abnormal0/3D_Printer/SolidWorks/New/铝型材角码/2020-210-45.SLDPRT

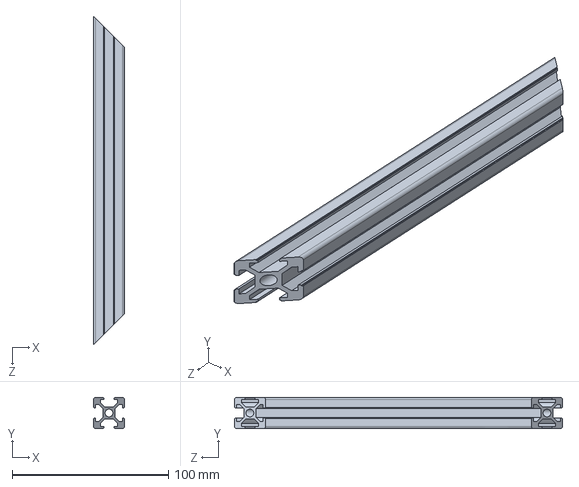
[picture p15: CAD file, 2020-09-15]
SolidWorks/New/铝型材角码/2020-210-45.SLDPRT
20.0 x 20.0 x 210.0 mm
