abnormal0/3D_Printer/SolidWorks/New/螺母座.SLDPRT

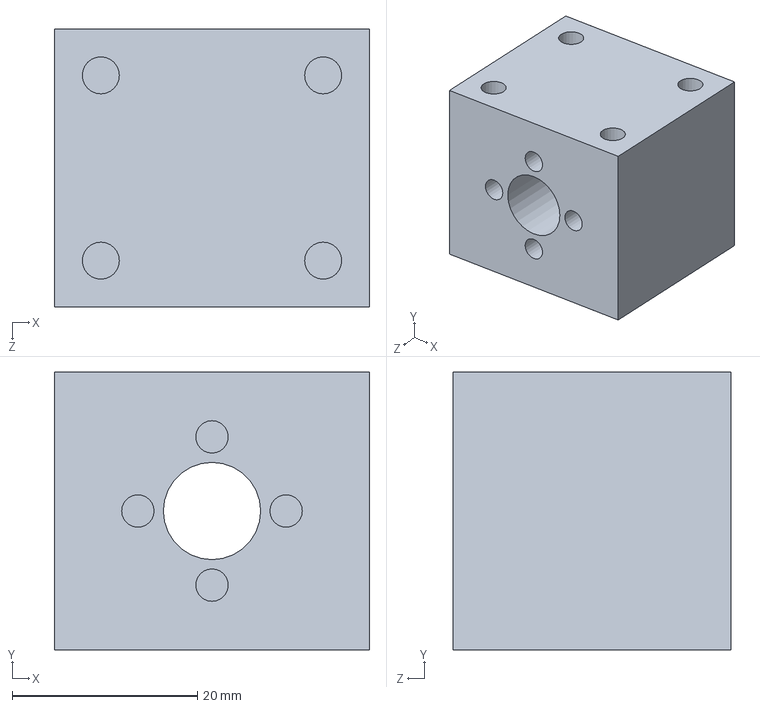
[picture p16: CAD file, 2020-09-15]
SolidWorks/New/螺母座.SLDPRT
34.0 x 30.0 x 30.0 mm
