abnormal0/3D_Printer/SolidWorks/New/铝型材角码/2020-188.SLDPRT

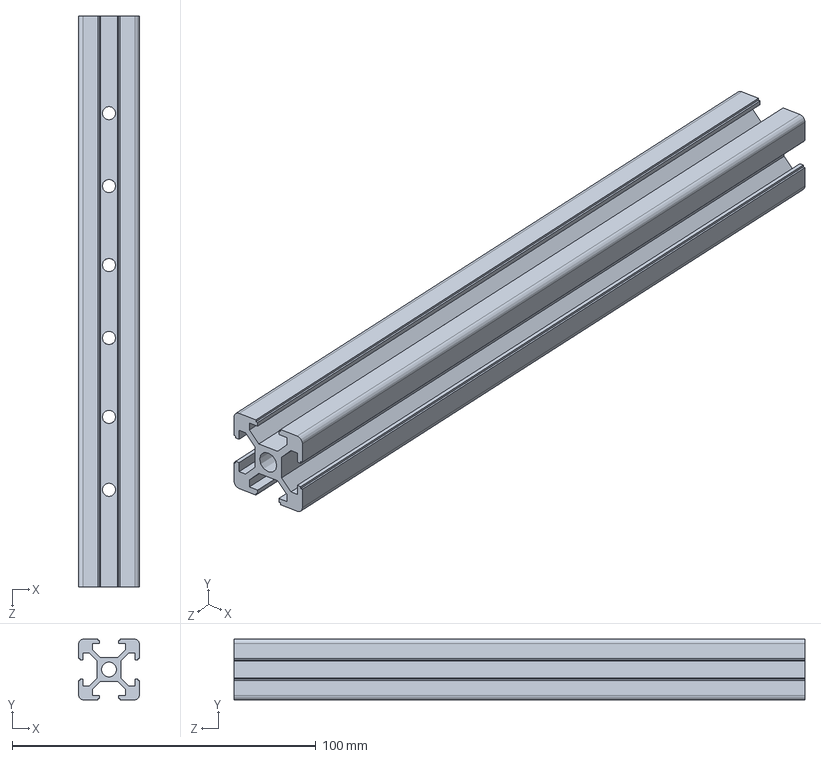
[picture p17: CAD file, 2020-09-15]
SolidWorks/New/铝型材角码/2020-188.SLDPRT
20.0 x 20.0 x 188.0 mm
