abnormal0/3D_Printer/SolidWorks/New/2020角码-45度.SLDPRT

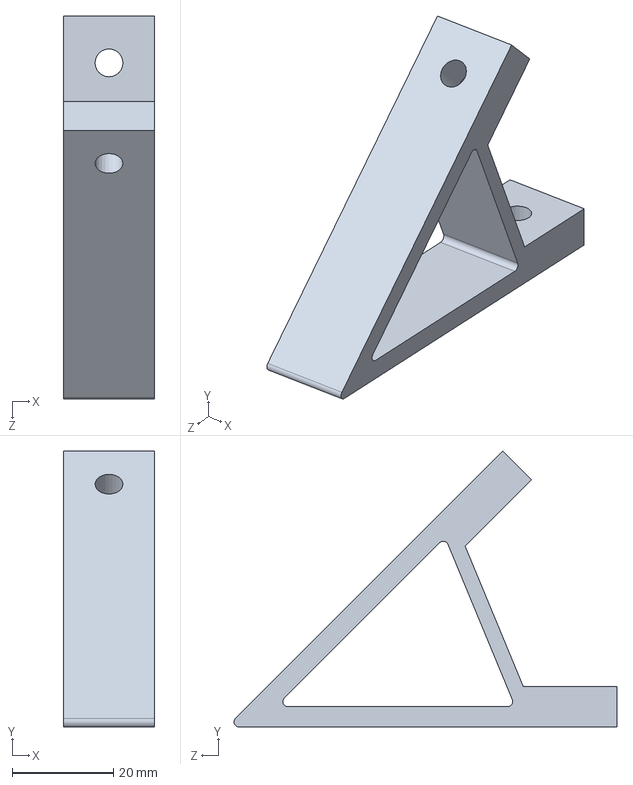
[picture p18: CAD file, 2020-09-15]
SolidWorks/New/2020角码-45度.SLDPRT
18.0 x 54.4 x 75.6 mm
