abnormal0/3D_Printer/SolidWorks/New/铝型材角码/2020-220.SLDPRT

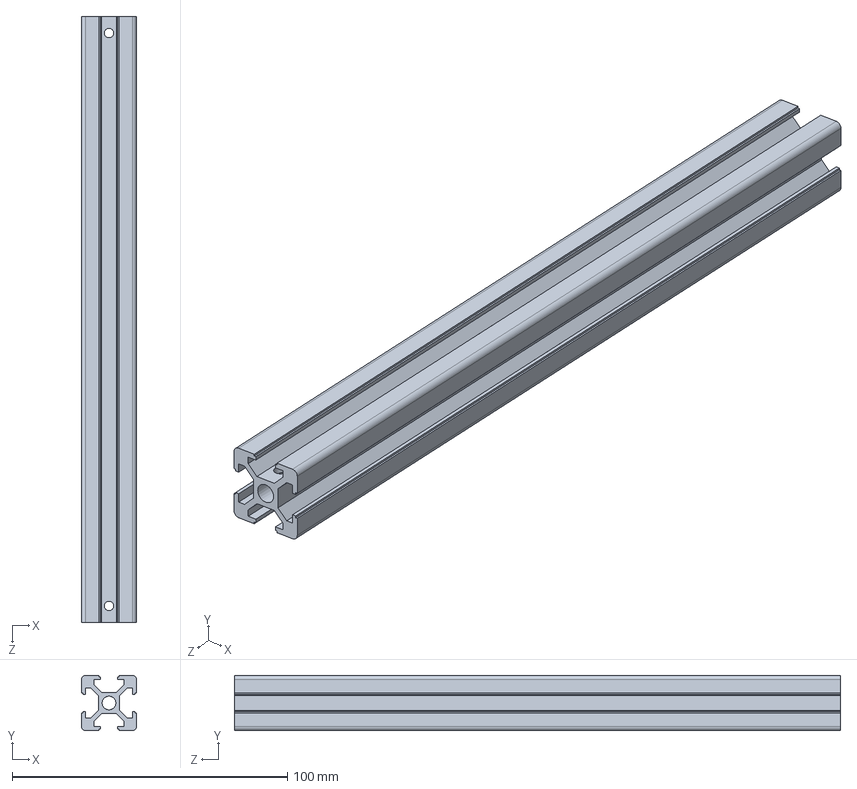
[picture p19: CAD file, 2020-09-15]
SolidWorks/New/铝型材角码/2020-220.SLDPRT
20.0 x 20.0 x 220.0 mm
