abnormal0/3D_Printer/SolidWorks/New/喷头安装座.SLDPRT

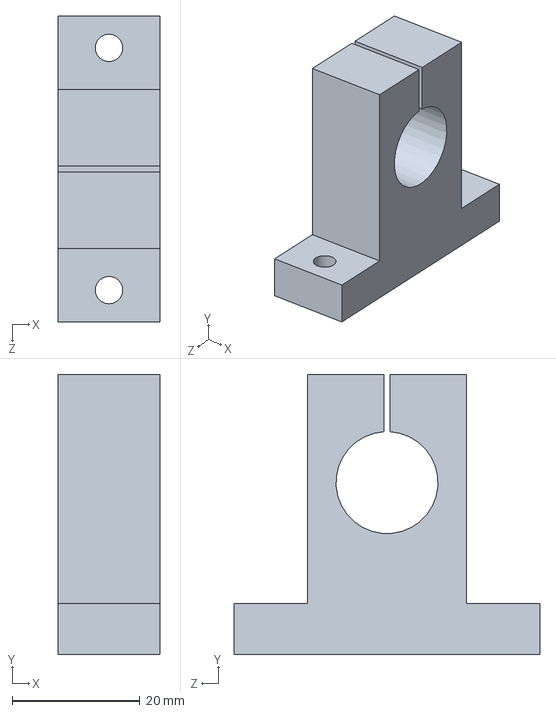
[picture p20: CAD file, 2020-09-15]
SolidWorks/New/喷头安装座.SLDPRT
16.0 x 44.0 x 48.0 mm
