abnormal0/3D_Printer/SolidWorks/New/M3蝶形螺母.SLDPRT

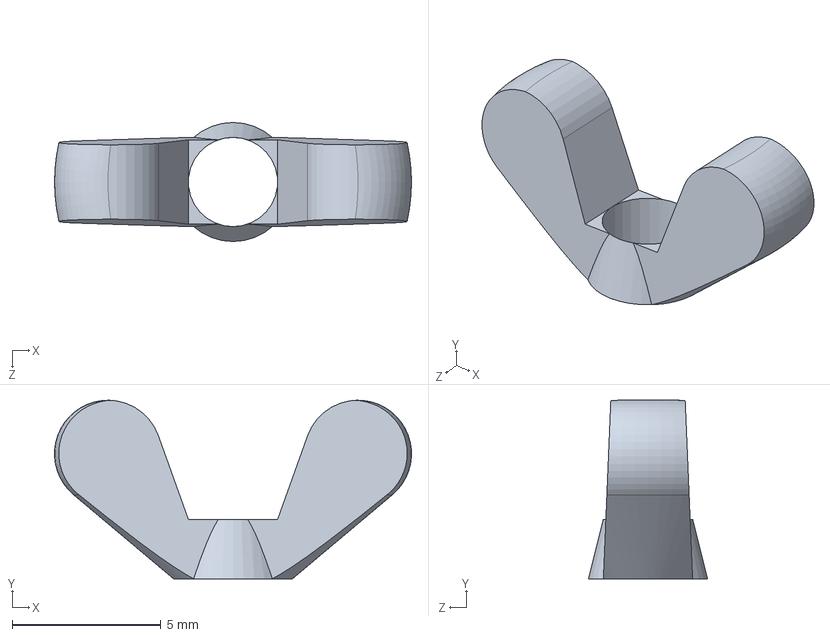
[picture p21: CAD file, 2020-09-15]
SolidWorks/New/M3蝶形螺母.SLDPRT
12.0 x 6.00 x 4.00 mm
