abnormal0/3D_Printer/SolidWorks/New/2GT-20齿同步轮.SLDPRT

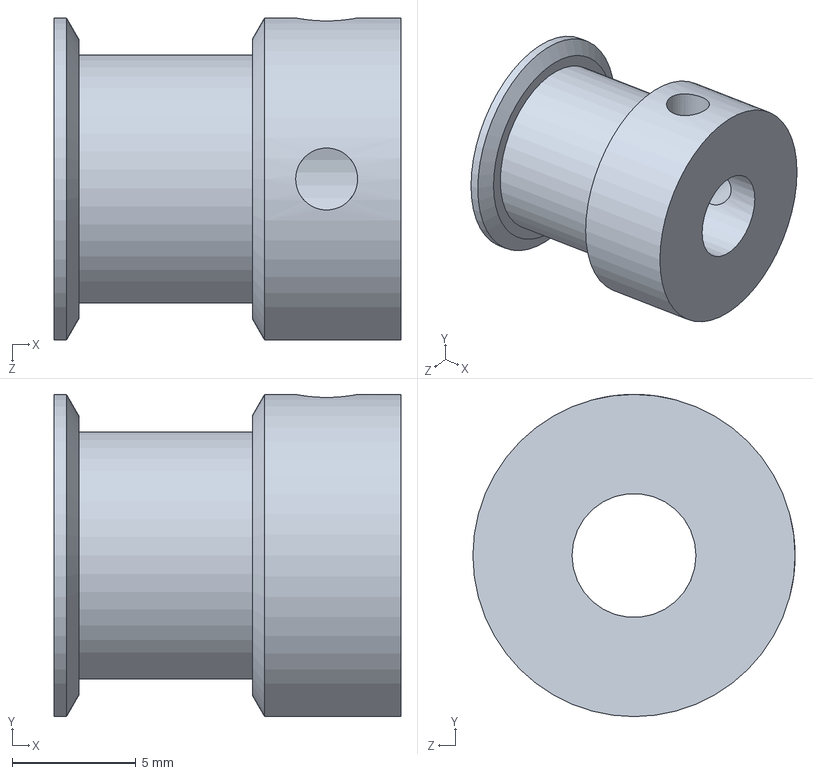
[picture p22: CAD file, 2020-09-15]
SolidWorks/New/2GT-20齿同步轮.SLDPRT
14.0 x 13.0 x 13.0 mm
