abnormal0/3D_Printer/SolidWorks/New/光杆架垫片.SLDPRT

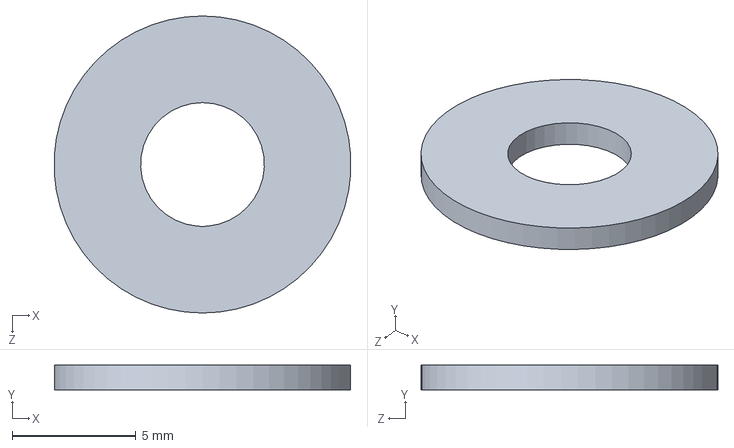
[picture p23: CAD file, 2020-09-15]
SolidWorks/New/光杆架垫片.SLDPRT
12.0 x 1.00 x 12.0 mm
