abnormal0/3D_Printer/SolidWorks/New/立式轴承座左铝片.SLDPRT

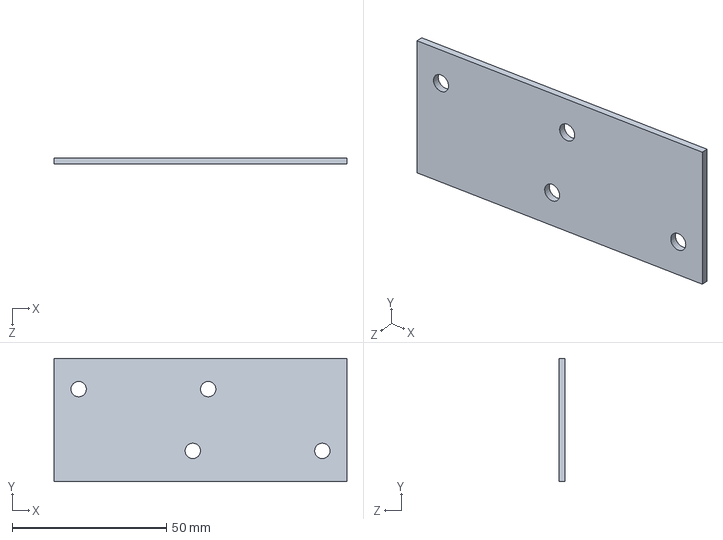
[picture p24: CAD file, 2020-09-15]
SolidWorks/New/立式轴承座左铝片.SLDPRT
95.0 x 40.0 x 2.00 mm
