abnormal0/3D_Printer/SolidWorks/New/小角件.SLDPRT

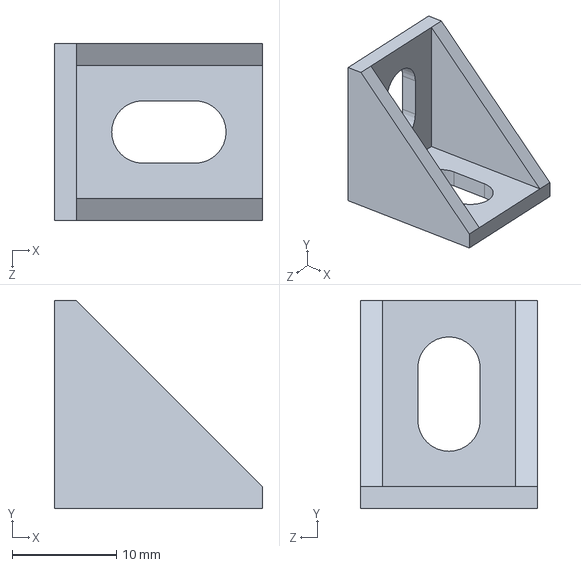
[picture p25: CAD file, 2020-09-15]
SolidWorks/New/小角件.SLDPRT
20.0 x 20.0 x 17.0 mm
