abnormal0/3D_Printer/SolidWorks/New/M3垫片.SLDPRT

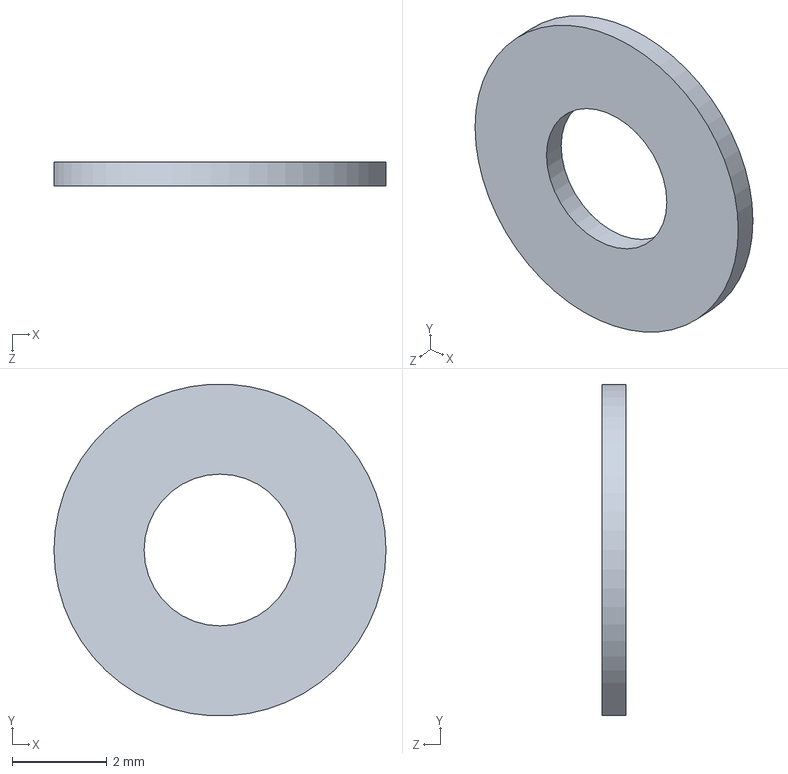
[picture p26: CAD file, 2020-09-15]
SolidWorks/New/M3垫片.SLDPRT
7.00 x 6.99 x 0.5 mm
