abnormal0/3D_Printer/SolidWorks/New/风扇.SLDPRT

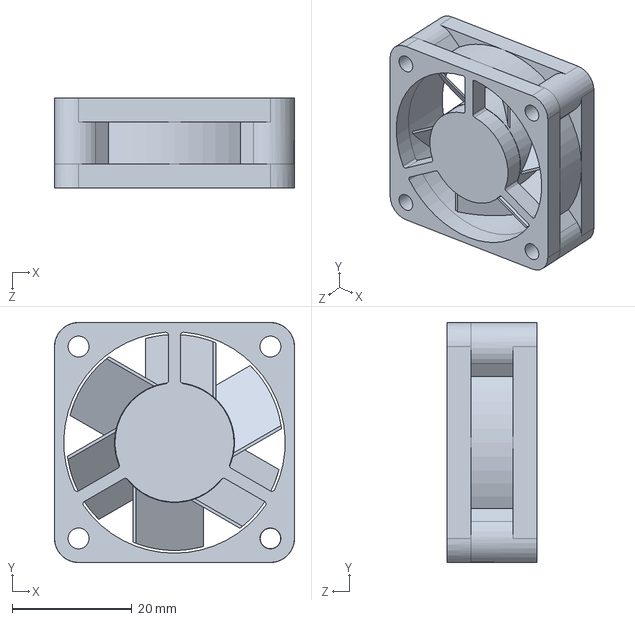
[picture p27: CAD file, 2020-09-15]
SolidWorks/New/风扇.SLDPRT
40.0 x 40.0 x 15.0 mm
