abnormal0/3D_Printer/SolidWorks/New/光电限位开关U型.SLDPRT

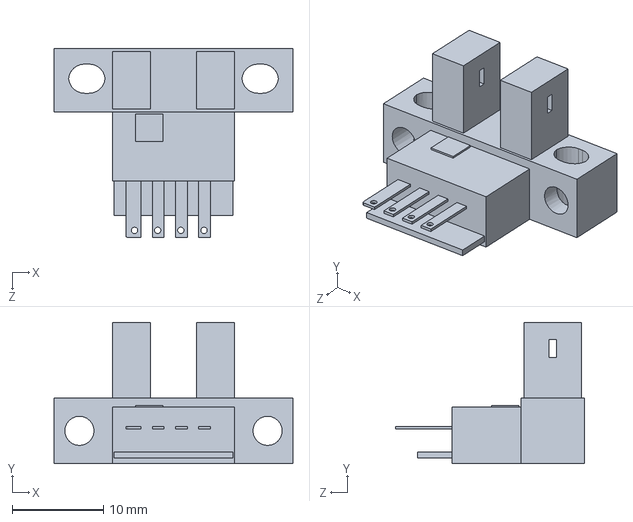
[picture p28: CAD file, 2020-09-15]
SolidWorks/New/光电限位开关U型.SLDPRT
26.2 x 15.5 x 20.7 mm
