abnormal0/3D_Printer/SolidWorks/New/直线轴承.SLDPRT

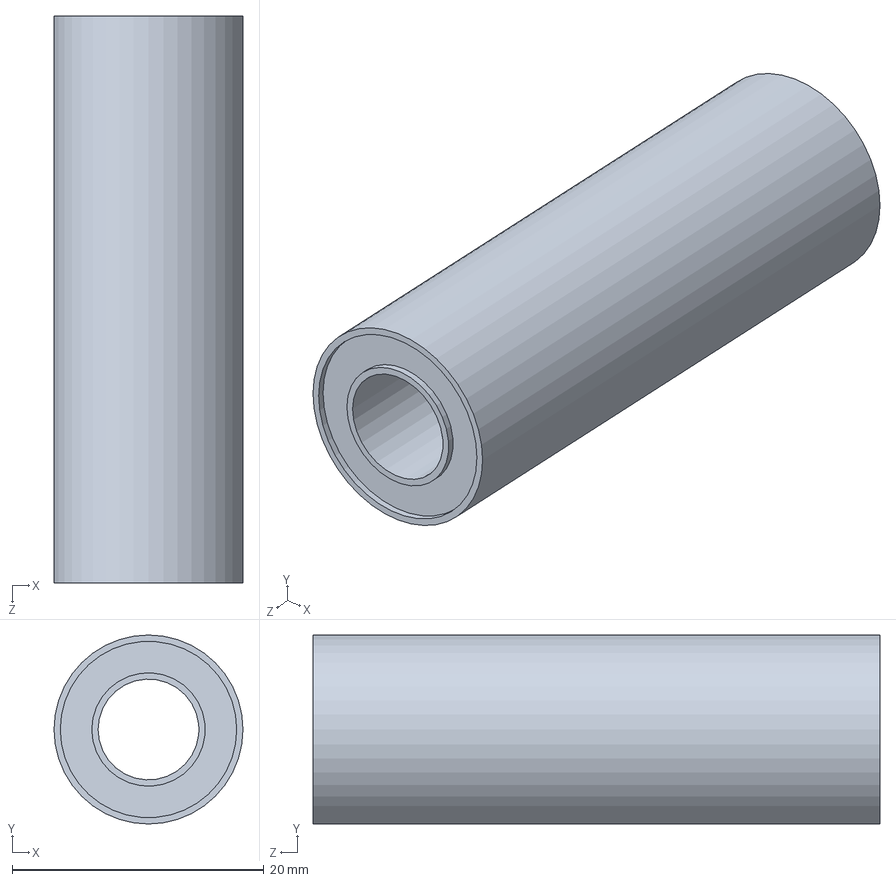
[picture p29: CAD file, 2020-09-15]
SolidWorks/New/直线轴承.SLDPRT
15.0 x 15.0 x 45.0 mm
