abnormal0/3D_Printer/SolidWorks/New/z轴限位片.SLDPRT

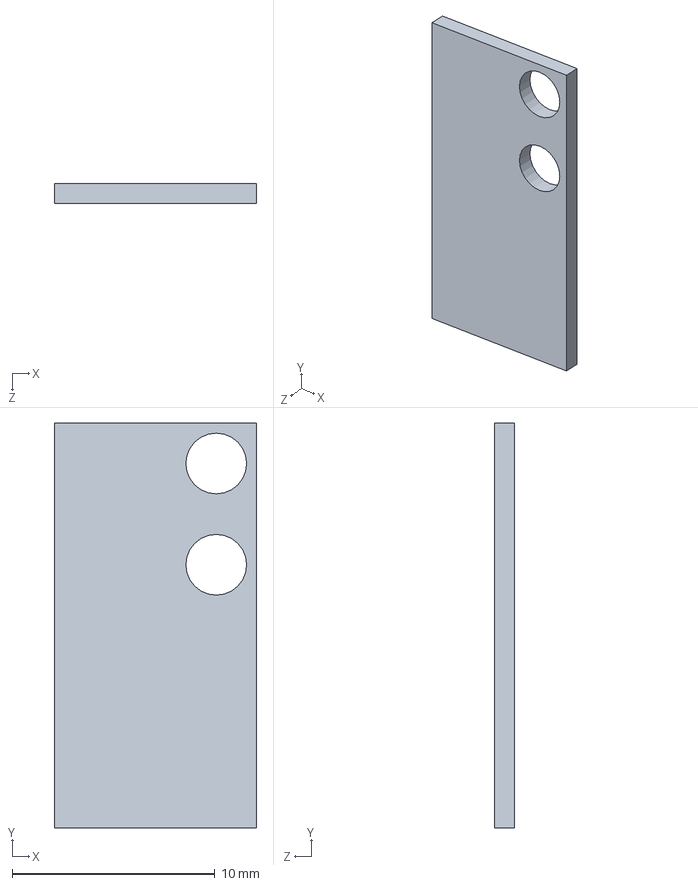
[picture p30: CAD file, 2020-09-15]
SolidWorks/New/z轴限位片.SLDPRT
10.0 x 20.0 x 1.00 mm
