abnormal0/3D_Printer/SolidWorks/New/螺母座z轴限位.SLDPRT

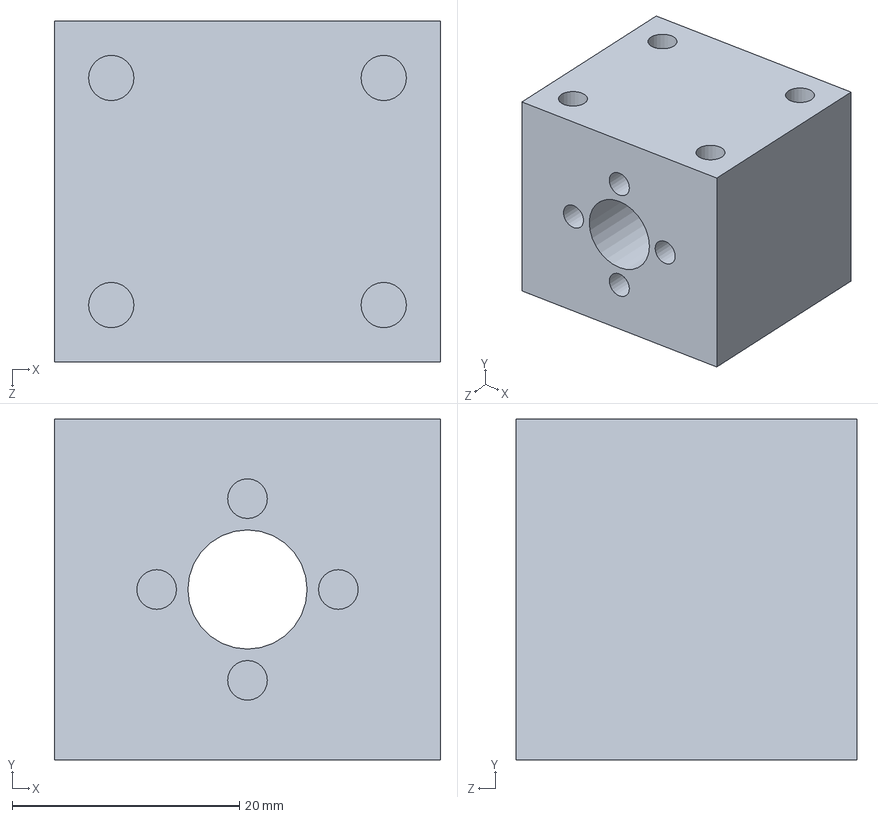
[picture p31: CAD file, 2020-09-15]
SolidWorks/New/螺母座z轴限位.SLDPRT
34.0 x 30.0 x 30.0 mm
