abnormal0/3D_Printer/SolidWorks/New/电机座.SLDPRT

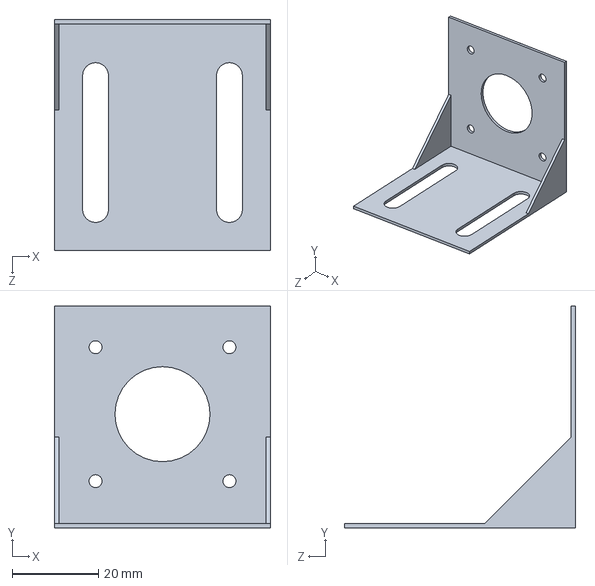
[picture p33: CAD file, 2020-09-15]
SolidWorks/New/电机座.SLDPRT
50.0 x 51.3 x 53.5 mm
