abnormal0/3D_Printer/SolidWorks/New/亚克力主板托盘.SLDPRT

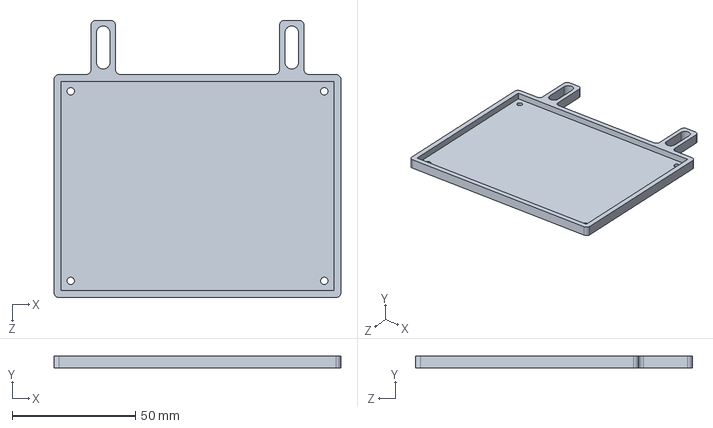
[picture p34: CAD file, 2020-09-15]
SolidWorks/New/亚克力主板托盘.SLDPRT
116.6 x 5.00 x 112.6 mm
