abnormal0/3D_Printer/SolidWorks/New/散热管.SLDPRT

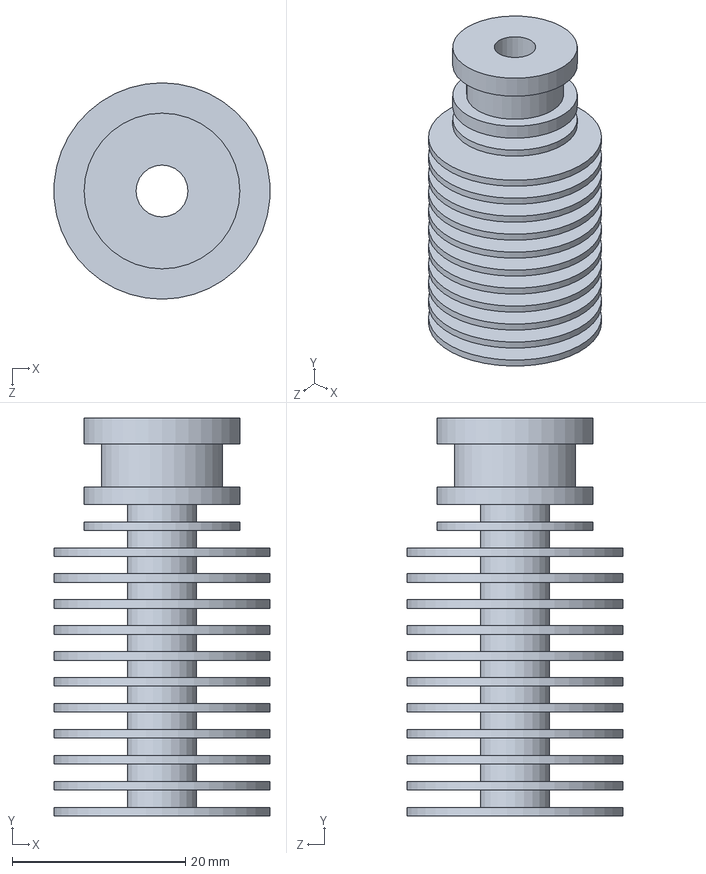
[picture p35: CAD file, 2020-09-15]
SolidWorks/New/散热管.SLDPRT
24.9 x 46.0 x 25.0 mm
