abnormal0/3D_Printer/SolidWorks/New/热床.SLDPRT

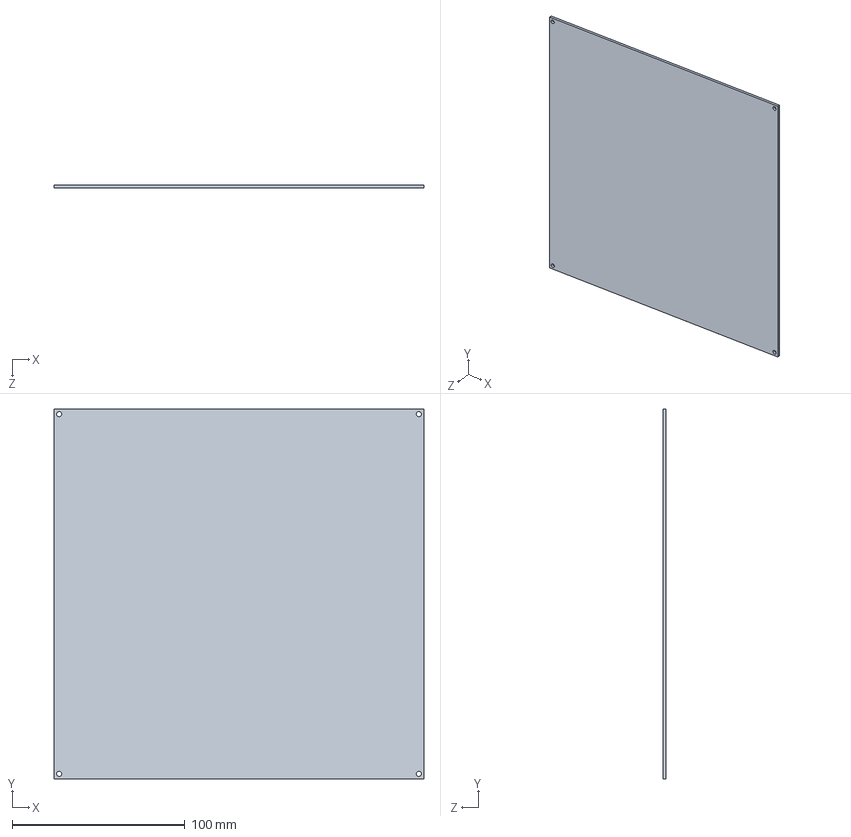
[picture p36: CAD file, 2020-09-15]
SolidWorks/New/热床.SLDPRT
214.0 x 214.0 x 2.00 mm
