abnormal0/3D_Printer/SolidWorks/New/直线轴承圆法兰.SLDPRT

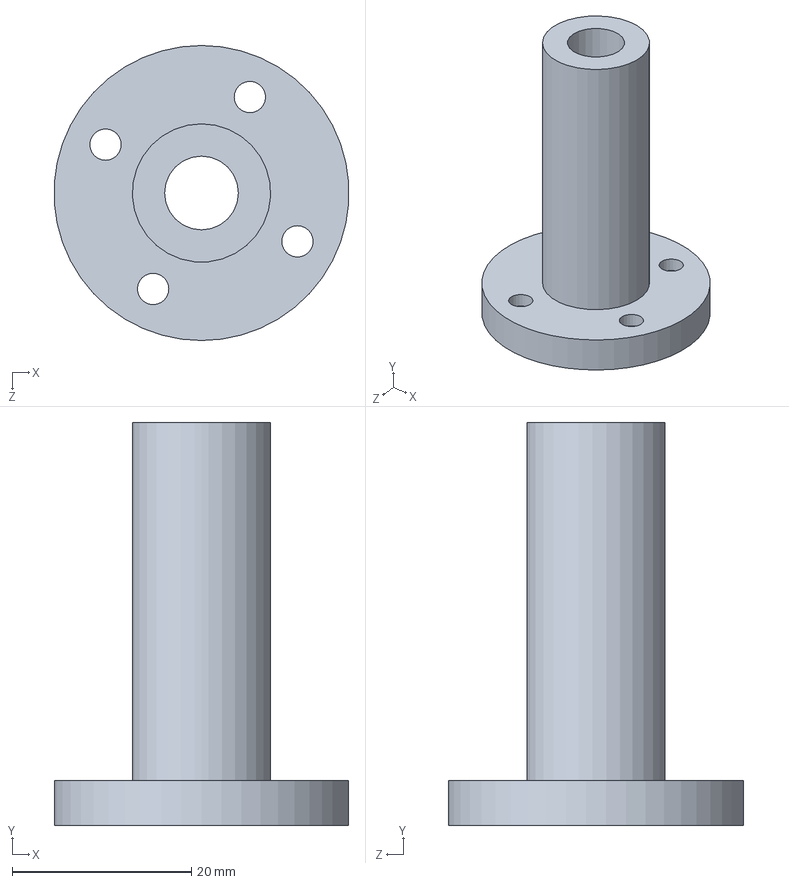
[picture p37: CAD file, 2020-09-15]
SolidWorks/New/直线轴承圆法兰.SLDPRT
32.9 x 45.0 x 32.9 mm
