abnormal0/3D_Printer/SolidWorks/New/丝轴z轴（无螺纹）.SLDPRT

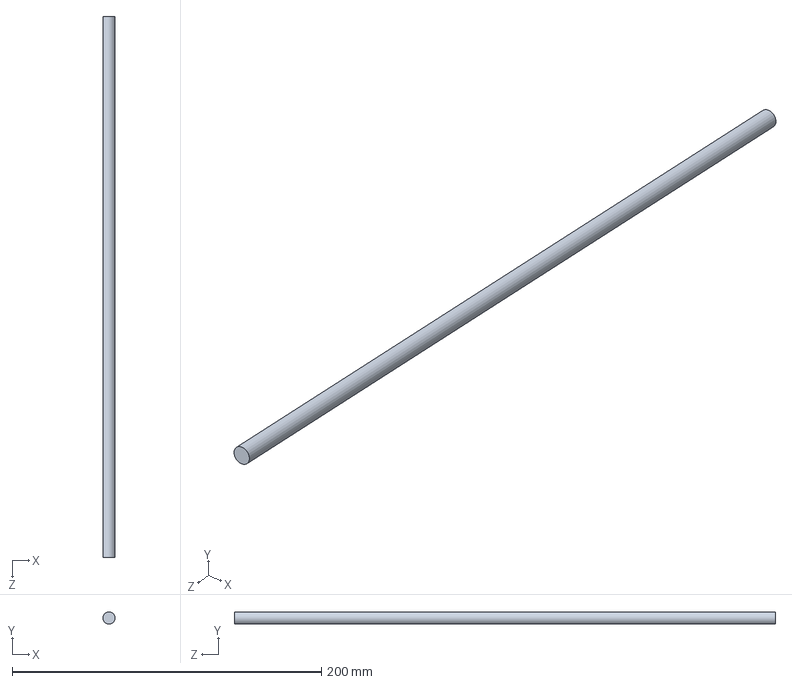
[picture p38: CAD file, 2020-09-15]
SolidWorks/New/丝轴z轴（无螺纹）.SLDPRT
8.00 x 8.00 x 350.0 mm
