abnormal0/3D_Printer/SolidWorks/New/M3_外六角螺丝.SLDPRT

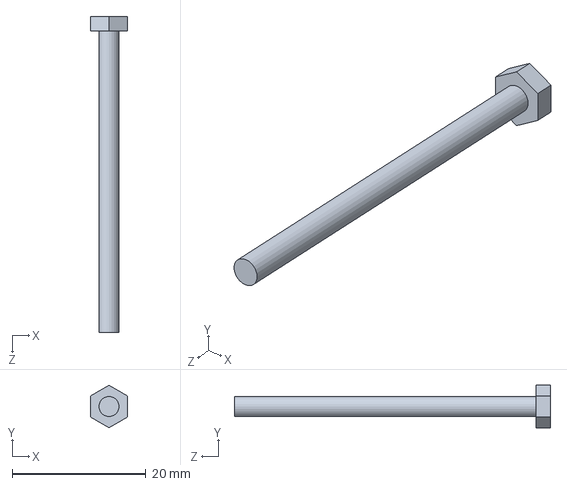
[picture p39: CAD file, 2020-09-15]
SolidWorks/New/M3_外六角螺丝.SLDPRT
5.50 x 6.35 x 47.2 mm
