abnormal0/3D_Printer/SolidWorks/New/2040-420.SLDPRT

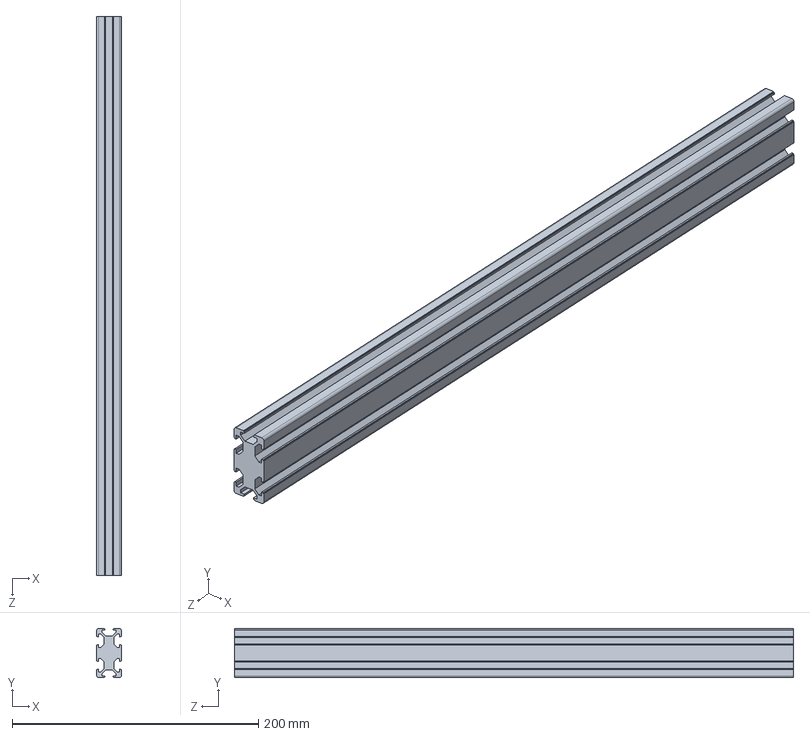
[picture p40: CAD file, 2020-09-15]
SolidWorks/New/2040-420.SLDPRT
20.0 x 40.0 x 454.0 mm
