abnormal0/3D_Printer/SolidWorks/New/M4船型螺母.SLDPRT

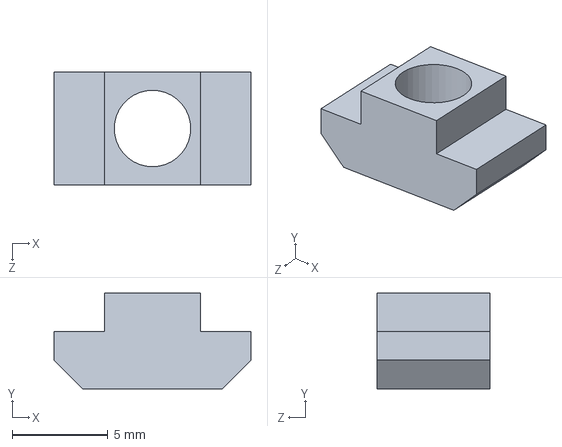
[picture p41: CAD file, 2020-09-15]
SolidWorks/New/M4船型螺母.SLDPRT
10.3 x 5.00 x 5.90 mm
