abnormal0/3D_Printer/SolidWorks/New/x轴铝片.SLDPRT

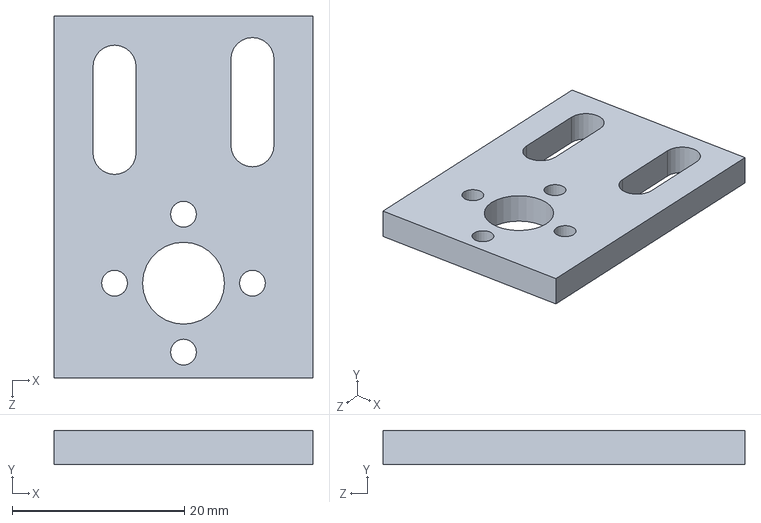
[picture p42: CAD file, 2020-09-15]
SolidWorks/New/x轴铝片.SLDPRT
30.0 x 4.00 x 42.0 mm
