abnormal0/3D_Printer/SolidWorks/New/同步带.SLDPRT

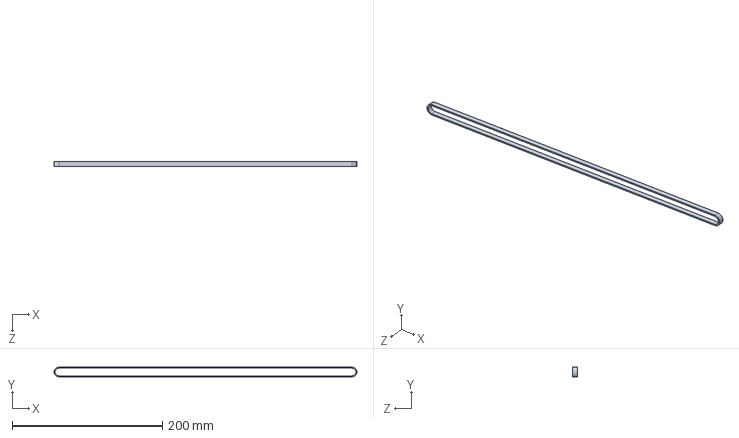
[picture p43: CAD file, 2020-09-15]
SolidWorks/New/同步带.SLDPRT
403.0 x 13.0 x 6.00 mm
