abnormal0/3D_Printer/SolidWorks/New/角铝.SLDPRT

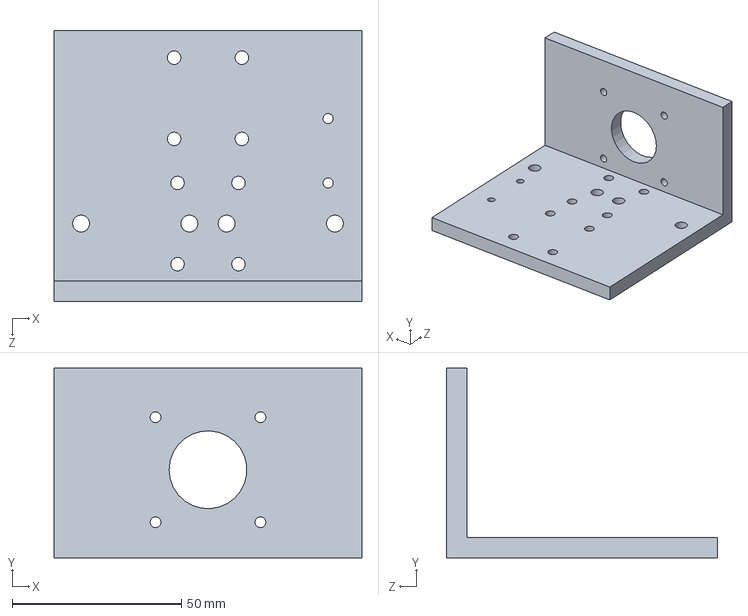
[picture p44: CAD file, 2020-09-15]
SolidWorks/New/角铝.SLDPRT
91.0 x 56.0 x 80.0 mm
