abnormal0/3D_Printer/SolidWorks/New/光杆架.SLDPRT

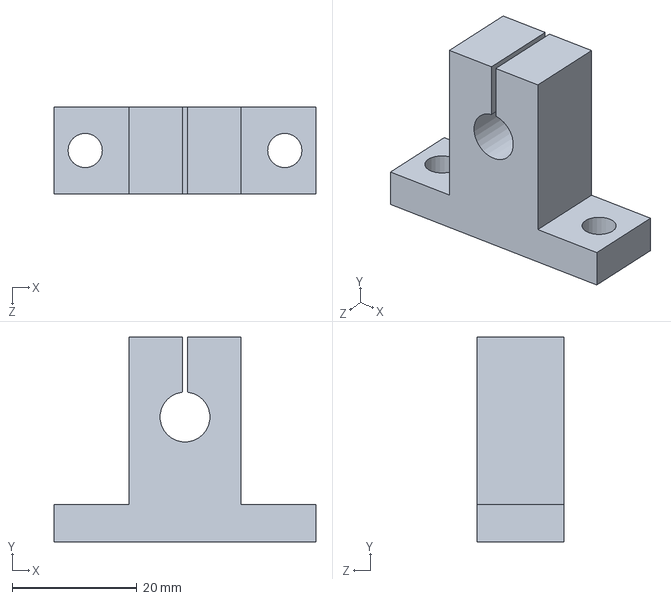
[picture p45: CAD file, 2020-09-15]
SolidWorks/New/光杆架.SLDPRT
42.0 x 32.8 x 14.0 mm
