abnormal0/3D_Printer/SolidWorks/New/42固定铝型材.SLDPRT

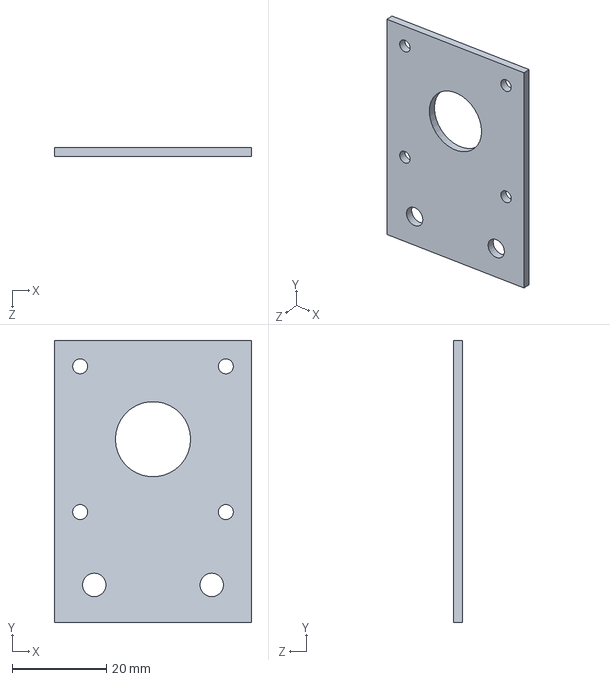
[picture p46: CAD file, 2020-09-15]
SolidWorks/New/42固定铝型材.SLDPRT
42.0 x 60.0 x 2.00 mm
