abnormal0/3D_Printer/SolidWorks/New/角铝中间.SLDPRT

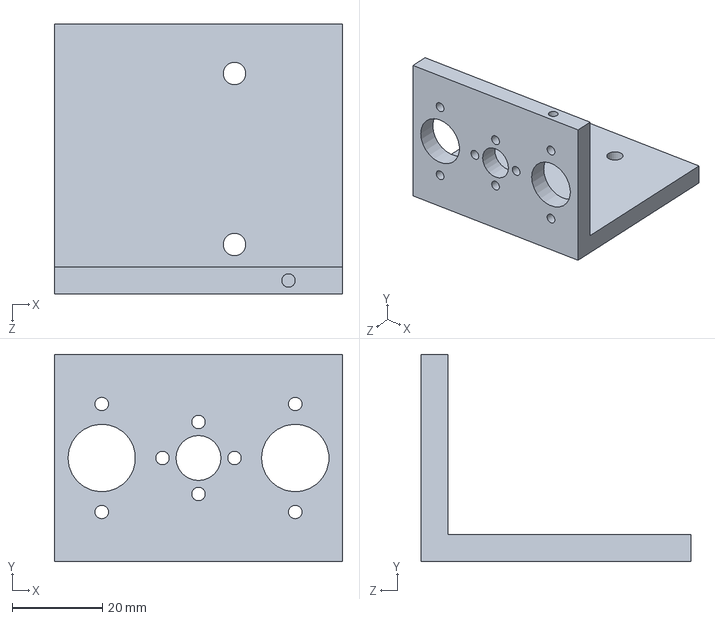
[picture p47: CAD file, 2020-09-15]
SolidWorks/New/角铝中间.SLDPRT
64.0 x 46.0 x 60.0 mm
