abnormal0/3D_Printer/SolidWorks/New/2020角码.SLDPRT

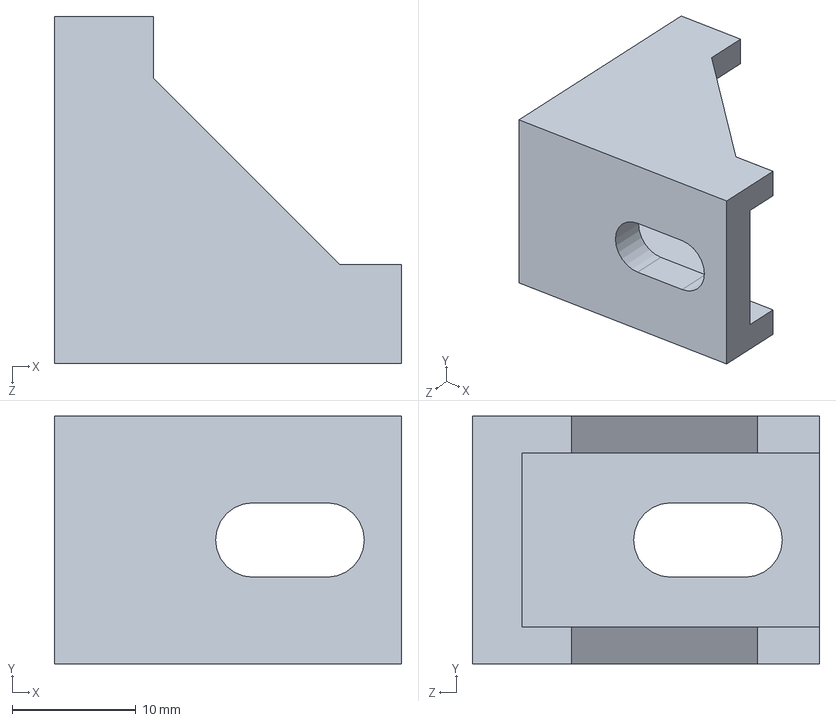
[picture p48: CAD file, 2020-09-15]
SolidWorks/New/2020角码.SLDPRT
28.0 x 20.0 x 28.0 mm
