abnormal0/3D_Printer/SolidWorks/New/喷嘴固定件.SLDPRT

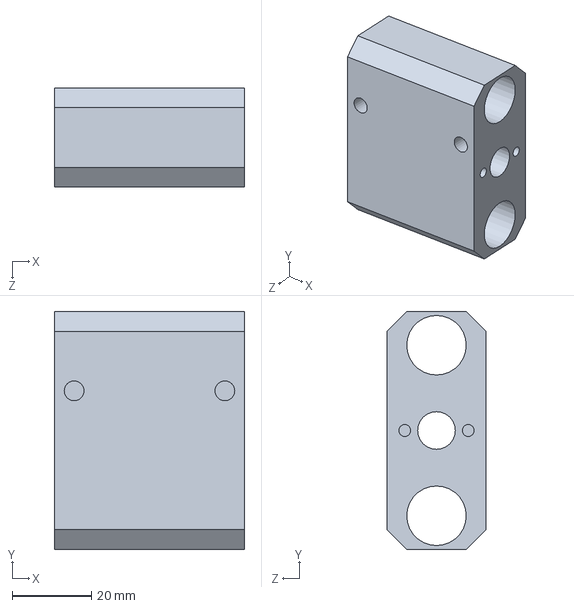
[picture p49: CAD file, 2020-09-15]
SolidWorks/New/喷嘴固定件.SLDPRT
48.0 x 60.0 x 25.0 mm
