abnormal0/3D_Printer/SolidWorks/New/卧式轴承座.SLDPRT

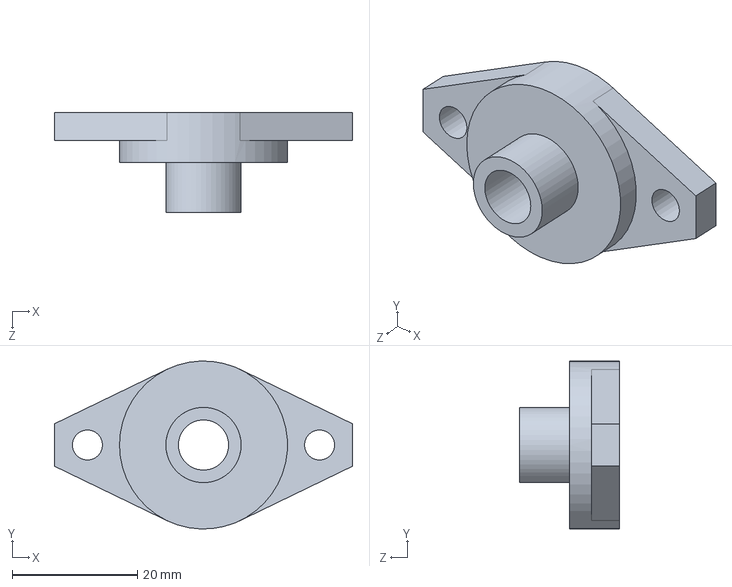
[picture p52: CAD file, 2020-09-15]
SolidWorks/New/卧式轴承座.SLDPRT
47.5 x 26.8 x 16.0 mm
