abnormal0/3D_Printer/SolidWorks/New/加热块.SLDPRT

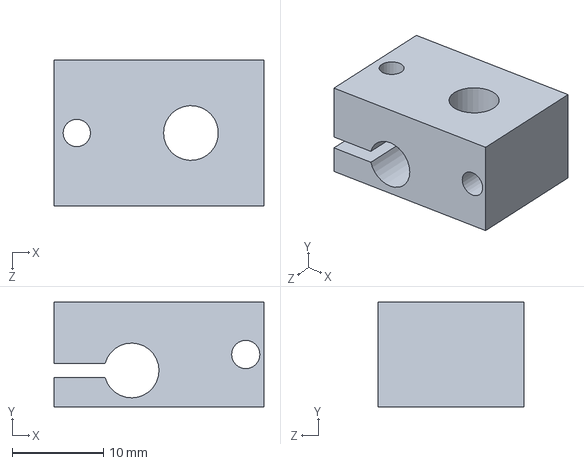
[picture p53: CAD file, 2020-09-15]
SolidWorks/New/加热块.SLDPRT
23.0 x 11.5 x 16.0 mm
