abnormal0/3D_Printer/SolidWorks/New/2020-300.SLDPRT

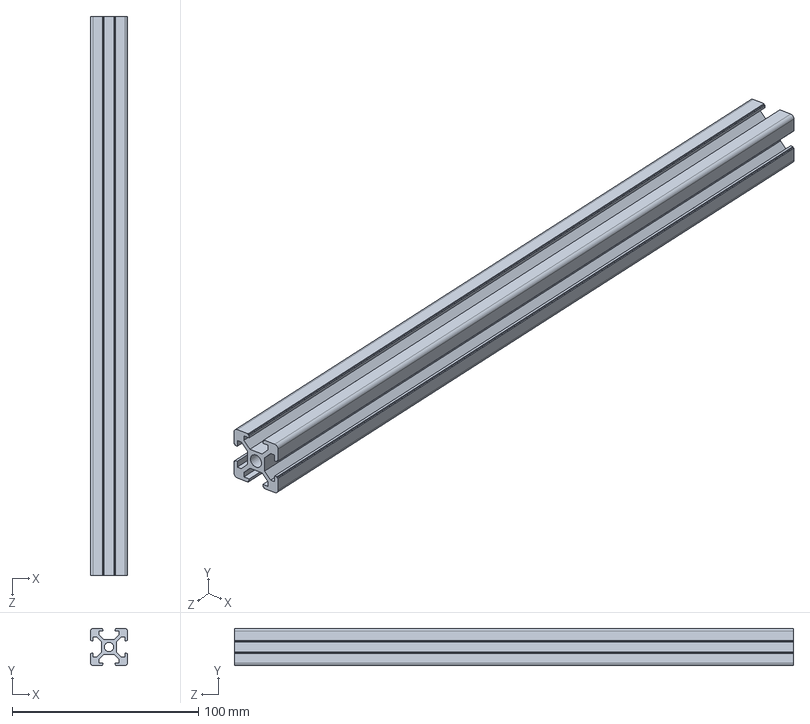
[picture p54: CAD file, 2020-09-15]
SolidWorks/New/2020-300.SLDPRT
20.0 x 20.0 x 300.0 mm
