abnormal0/3D_Printer/SolidWorks/New/光杆x轴.SLDPRT

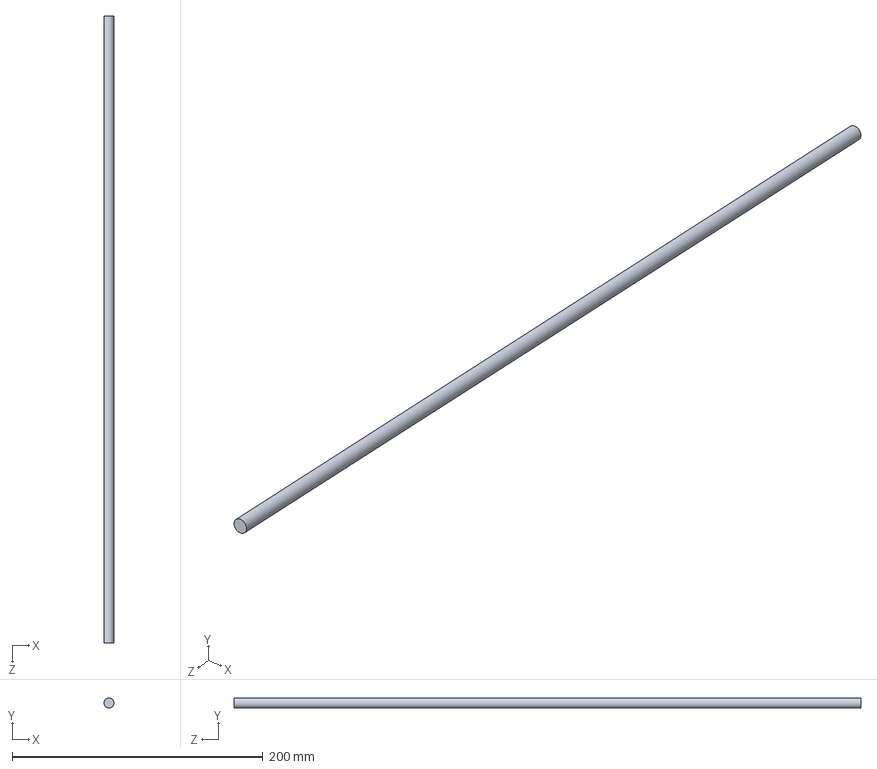
[picture p55: CAD file, 2020-09-15]
SolidWorks/New/光杆x轴.SLDPRT
8.00 x 8.00 x 500.0 mm
