abnormal0/3D_Printer/SolidWorks/New/2020-290.SLDPRT

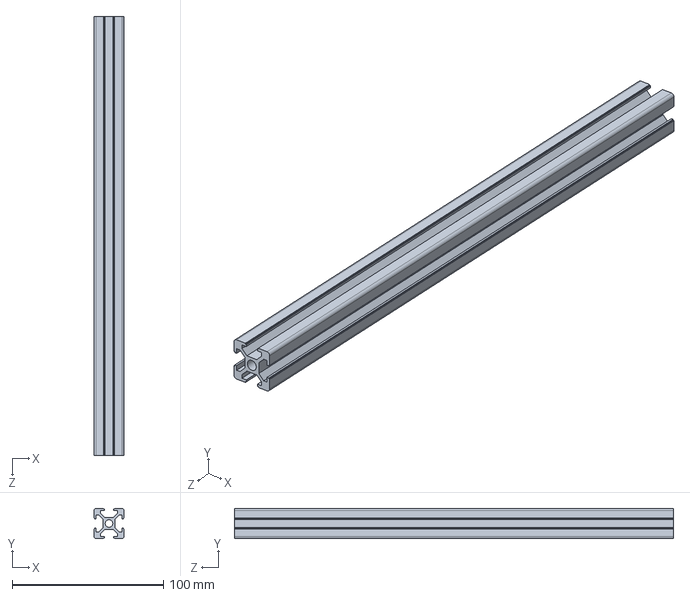
[picture p56: CAD file, 2020-09-15]
SolidWorks/New/2020-290.SLDPRT
20.0 x 20.0 x 290.0 mm
