abnormal0/3D_Printer/SolidWorks/New/42 motor.SLDPRT

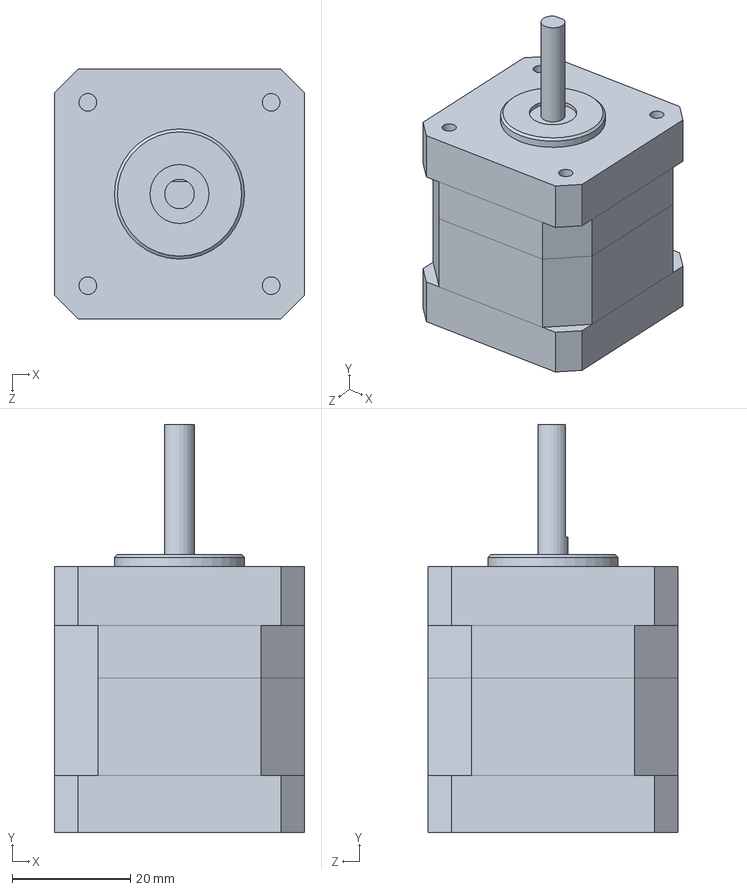
[picture p57: CAD file, 2020-09-15]
SolidWorks/New/42 motor.SLDPRT
42.3 x 69.0 x 42.3 mm
