abnormal0/3D_Printer/SolidWorks/New/风扇3010.SLDPRT

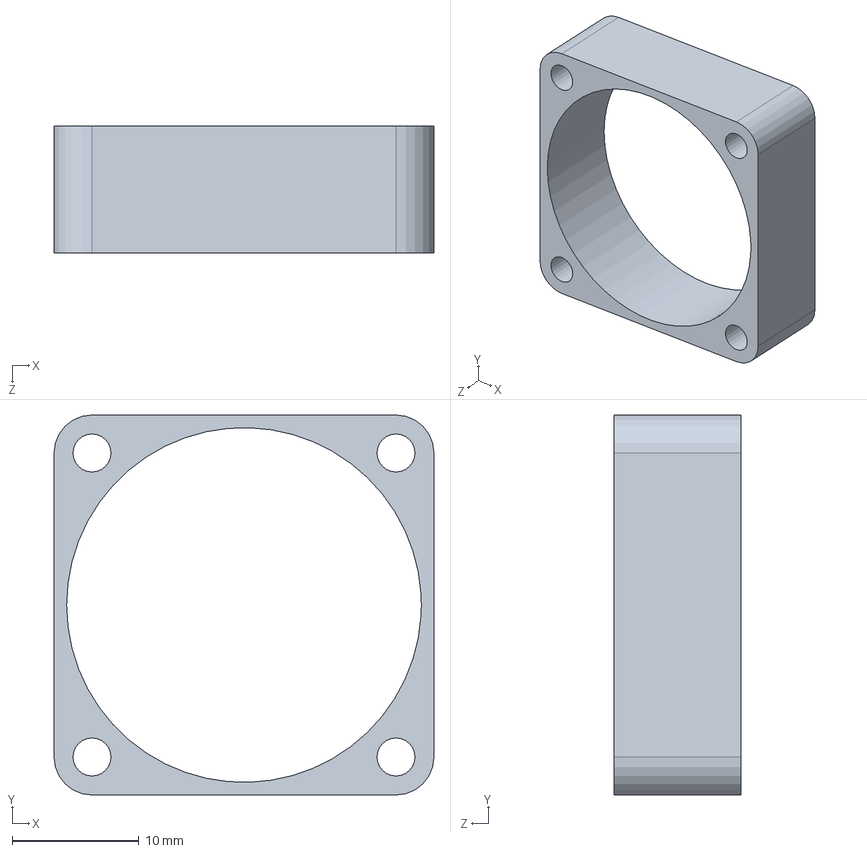
[picture p58: CAD file, 2020-09-15]
SolidWorks/New/风扇3010.SLDPRT
30.0 x 30.0 x 10.0 mm
