abnormal0/3D_Printer/SolidWorks/New/丝杆螺母.SLDPRT

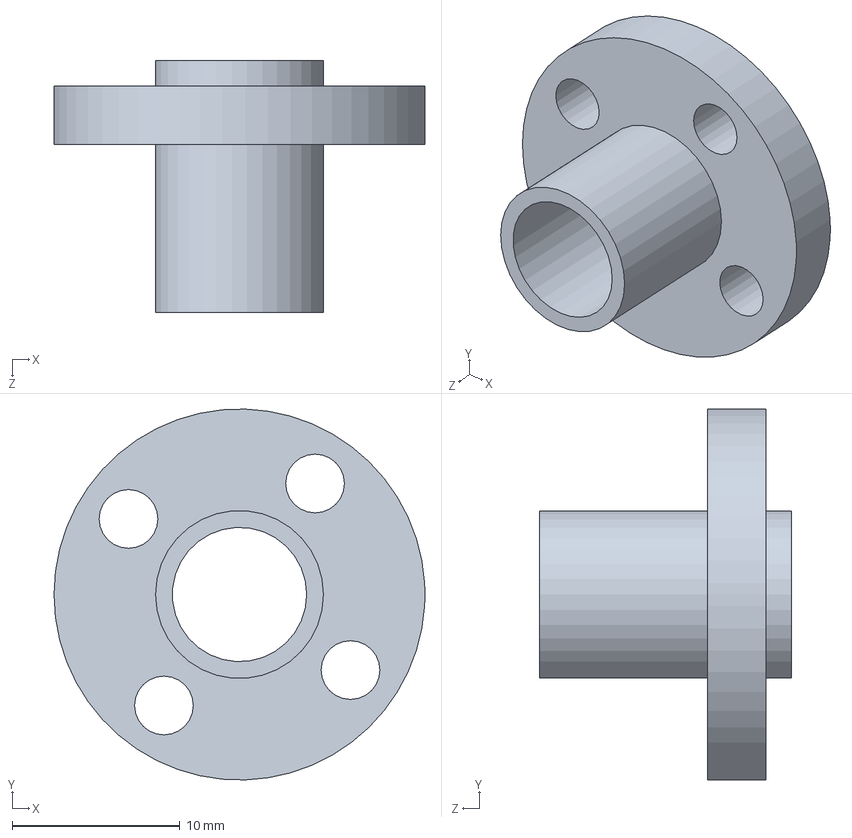
[picture p59: CAD file, 2020-09-15]
SolidWorks/New/丝杆螺母.SLDPRT
22.1 x 22.1 x 15.0 mm
