abnormal0/3D_Printer/SolidWorks/New/椭圆直线轴承.SLDPRT

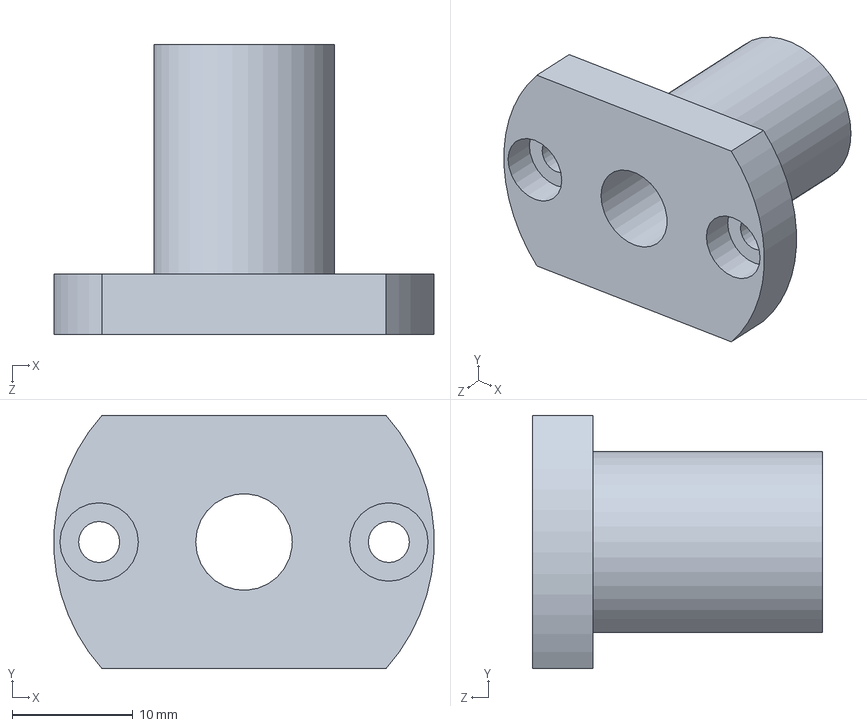
[picture p60: CAD file, 2020-09-15]
SolidWorks/New/椭圆直线轴承.SLDPRT
31.5 x 21.0 x 24.0 mm
