abnormal0/3D_Printer/SolidWorks/New/玻璃板200-200-4.SLDPRT

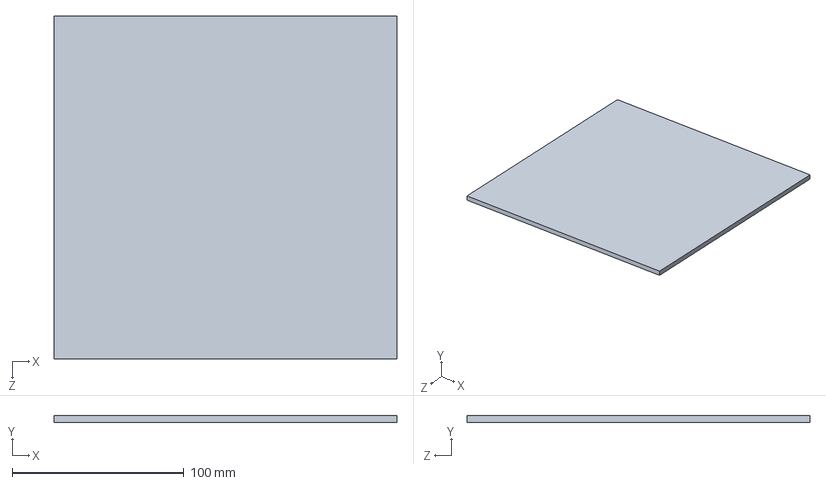
[picture p61: CAD file, 2020-09-15]
SolidWorks/New/玻璃板200-200-4.SLDPRT
200.0 x 4.00 x 200.0 mm
