abnormal0/3D_Printer/SolidWorks/New/喷头.SLDPRT

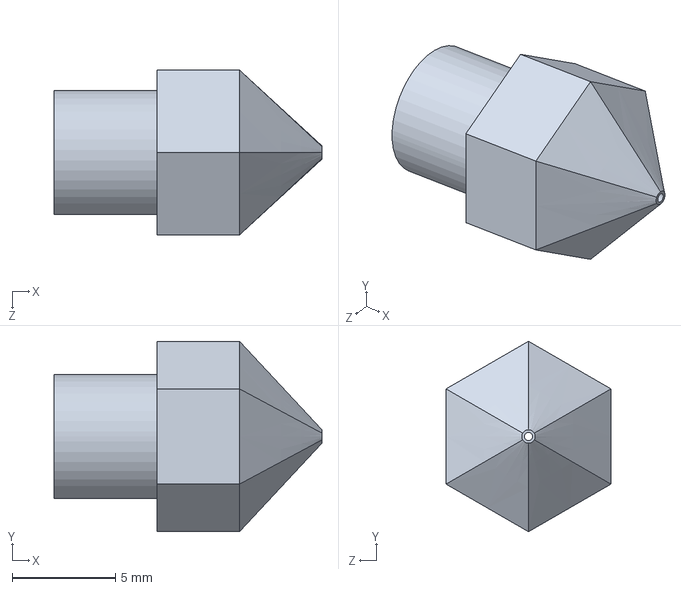
[picture p62: CAD file, 2020-09-15]
SolidWorks/New/喷头.SLDPRT
13.0 x 9.24 x 8.00 mm
