abnormal0/3D_Printer/SolidWorks/New/光电限位开关.SLDPRT

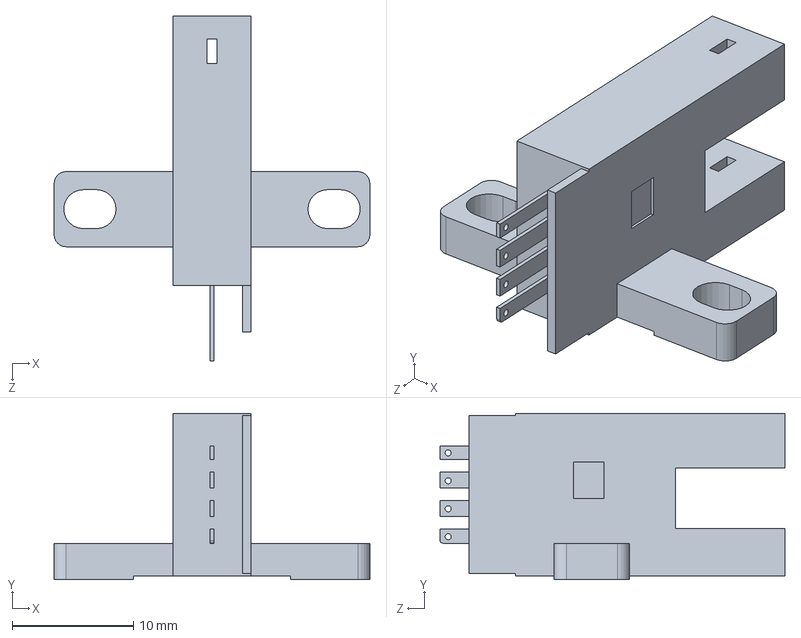
[picture p63: CAD file, 2020-09-15]
SolidWorks/New/光电限位开关.SLDPRT
26.0 x 13.7 x 28.4 mm
