abnormal0/3D_Printer/SolidWorks/New/2040-290.SLDPRT

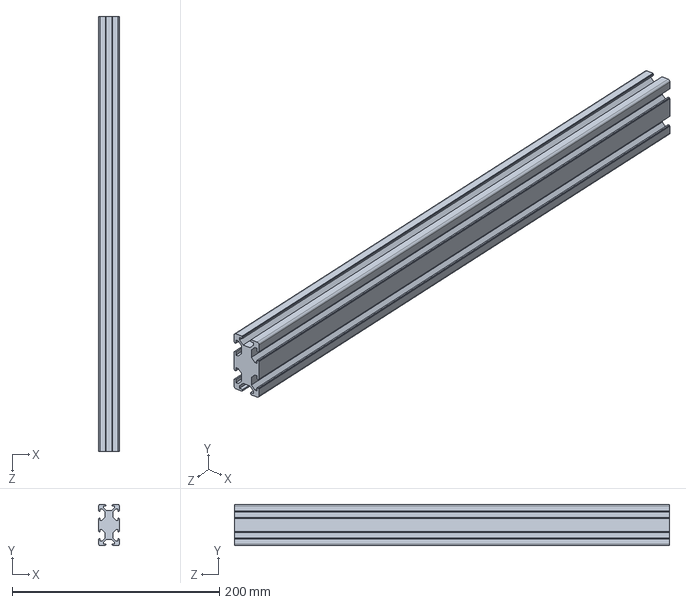
[picture p64: CAD file, 2020-09-15]
SolidWorks/New/2040-290.SLDPRT
20.0 x 40.0 x 420.0 mm
