abnormal0/3D_Printer/SolidWorks/New/立式轴承座下铝片.SLDPRT

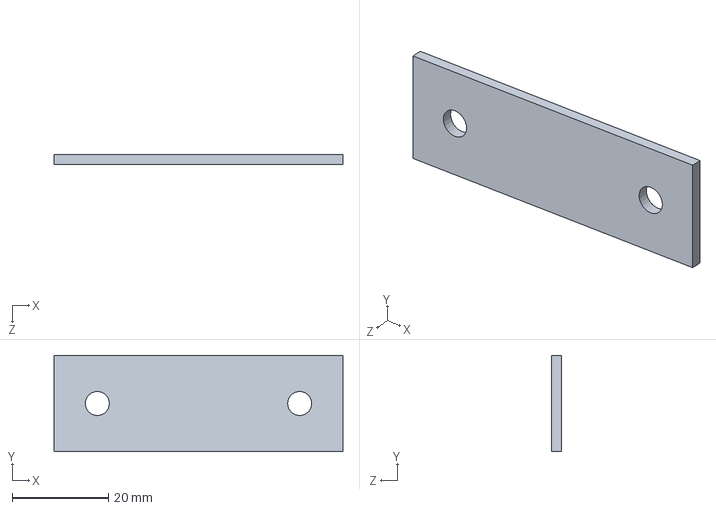
[picture p65: CAD file, 2020-09-15]
SolidWorks/New/立式轴承座下铝片.SLDPRT
60.0 x 20.0 x 2.00 mm
