abnormal0/3D_Printer/SolidWorks/New/直线光杆滑轨.SLDPRT

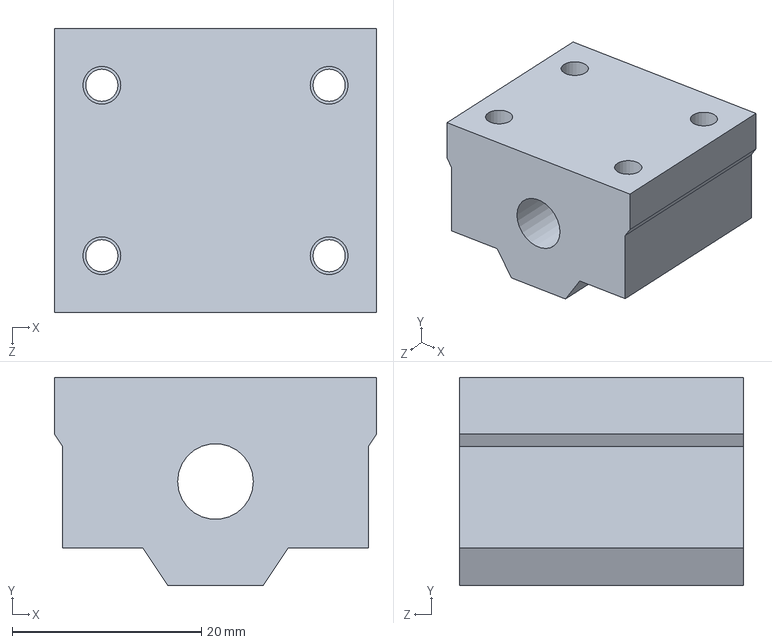
[picture p66: CAD file, 2020-09-15]
SolidWorks/New/直线光杆滑轨.SLDPRT
34.0 x 22.0 x 30.0 mm
