abnormal0/3D_Printer/SolidWorks/New/风扇固定片.SLDPRT

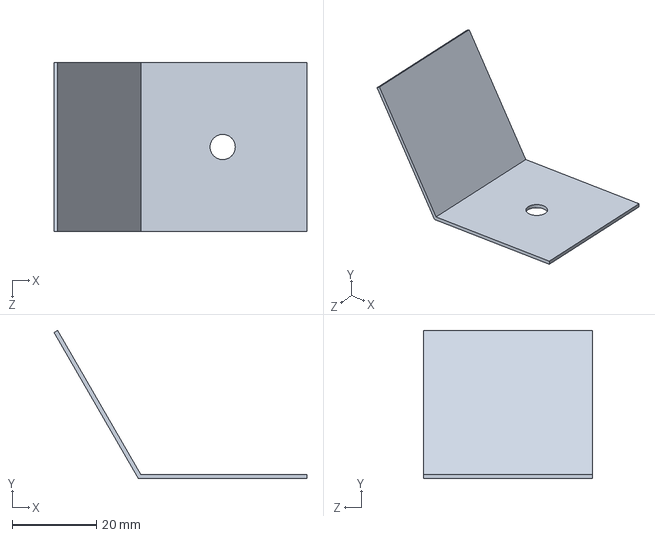
[picture p67: CAD file, 2020-09-15]
SolidWorks/New/风扇固定片.SLDPRT
60.0 x 35.1 x 40.0 mm
