abnormal0/3D_Printer/SolidWorks/New/角铝右侧.SLDPRT

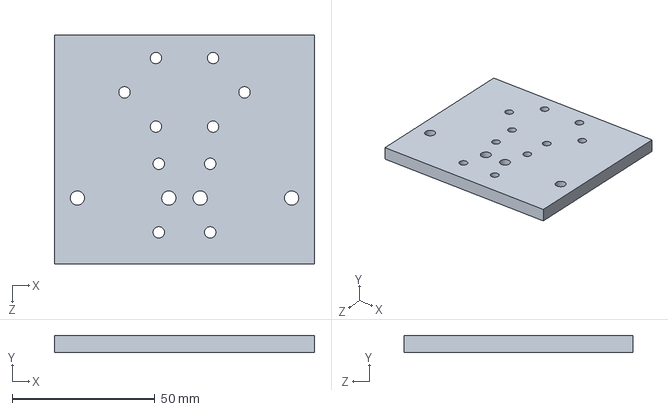
[picture p68: CAD file, 2020-09-15]
SolidWorks/New/角铝右侧.SLDPRT
91.0 x 6.00 x 80.0 mm
