abnormal0/3D_Printer/SolidWorks/New/x轴限位片.SLDPRT

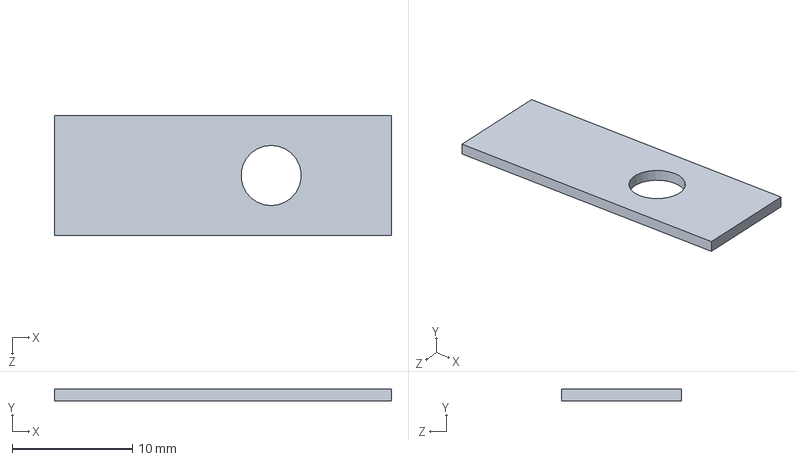
[picture p69: CAD file, 2020-09-15]
SolidWorks/New/x轴限位片.SLDPRT
28.0 x 1.00 x 10.0 mm
