abnormal0/3D_Printer/SolidWorks/New/光杆Y轴.SLDPRT

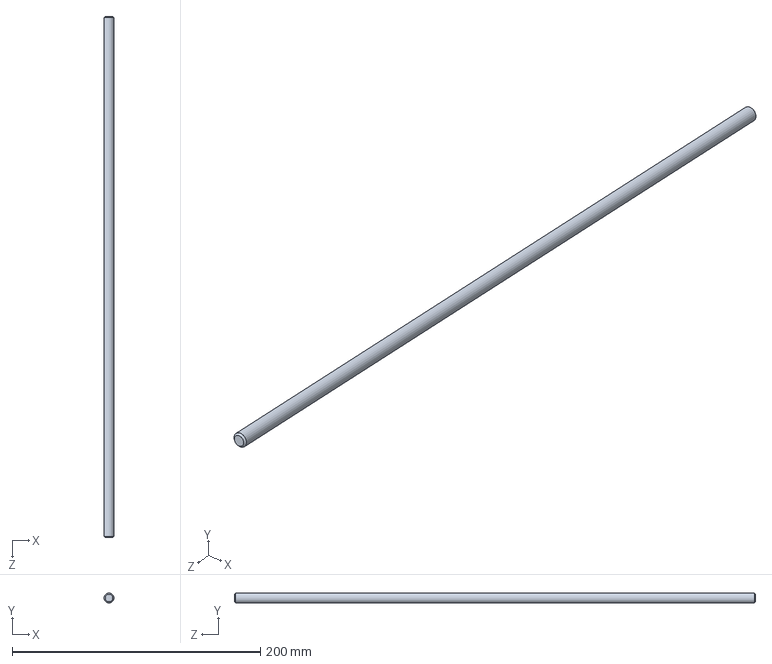
[picture p70: CAD file, 2020-09-15]
SolidWorks/New/光杆Y轴.SLDPRT
8.00 x 8.00 x 420.0 mm
