abnormal0/3D_Printer/SolidWorks/New/光杆z轴.SLDPRT

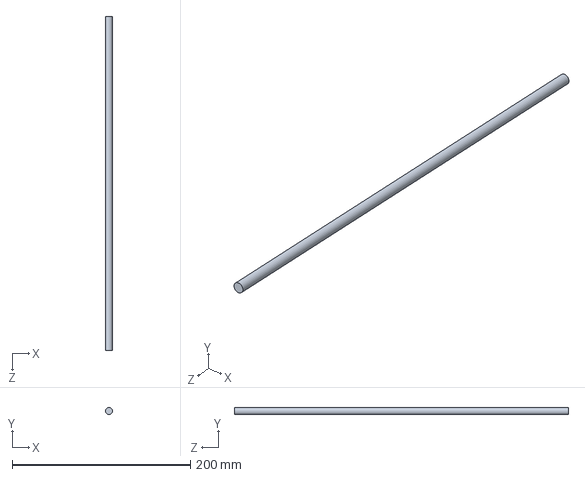
[picture p71: CAD file, 2020-09-15]
SolidWorks/New/光杆z轴.SLDPRT
8.00 x 8.00 x 375.0 mm
