abnormal0/3D_Printer/SolidWorks/New/立式轴承座.SLDPRT

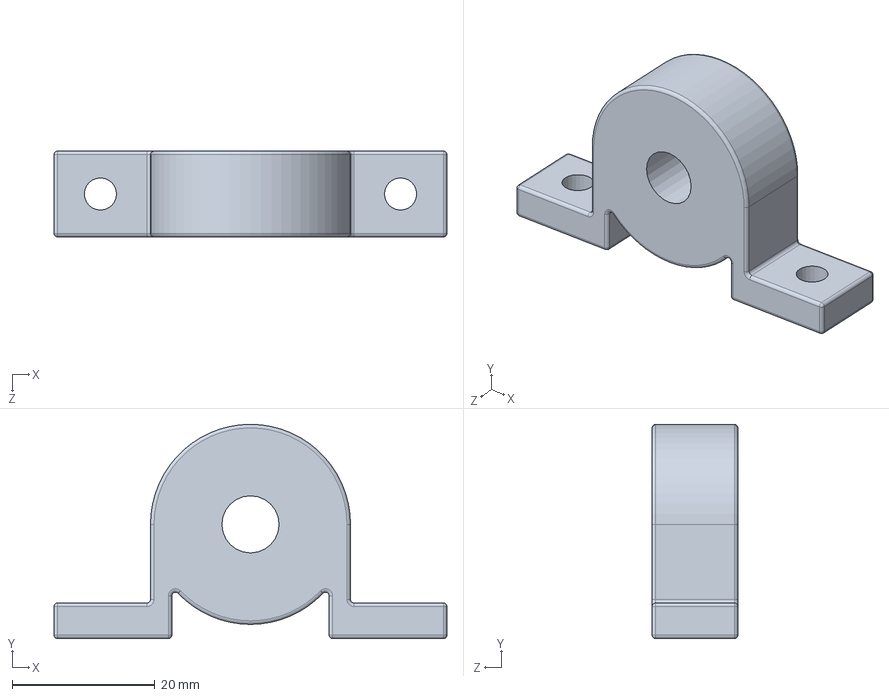
[picture p72: CAD file, 2020-09-15]
SolidWorks/New/立式轴承座.SLDPRT
55.0 x 30.0 x 12.0 mm
