abnormal0/3D_Printer/SolidWorks/New/y轴限位片.SLDPRT

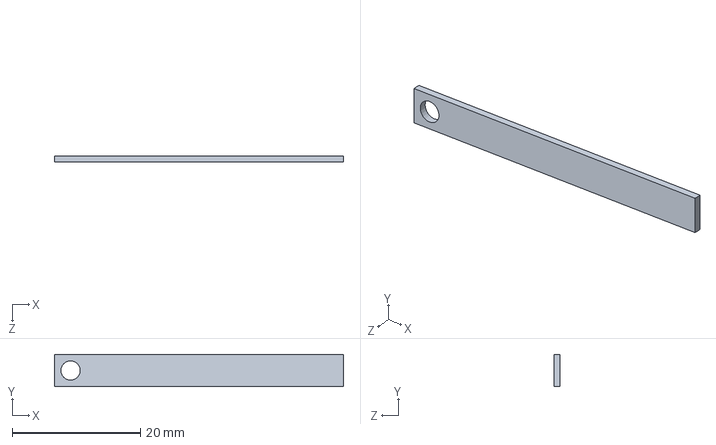
[picture p73: CAD file, 2020-09-15]
SolidWorks/New/y轴限位片.SLDPRT
45.0 x 5.00 x 1.00 mm
