abnormal0/3D_Printer/SolidWorks/New/风扇固定.SLDPRT

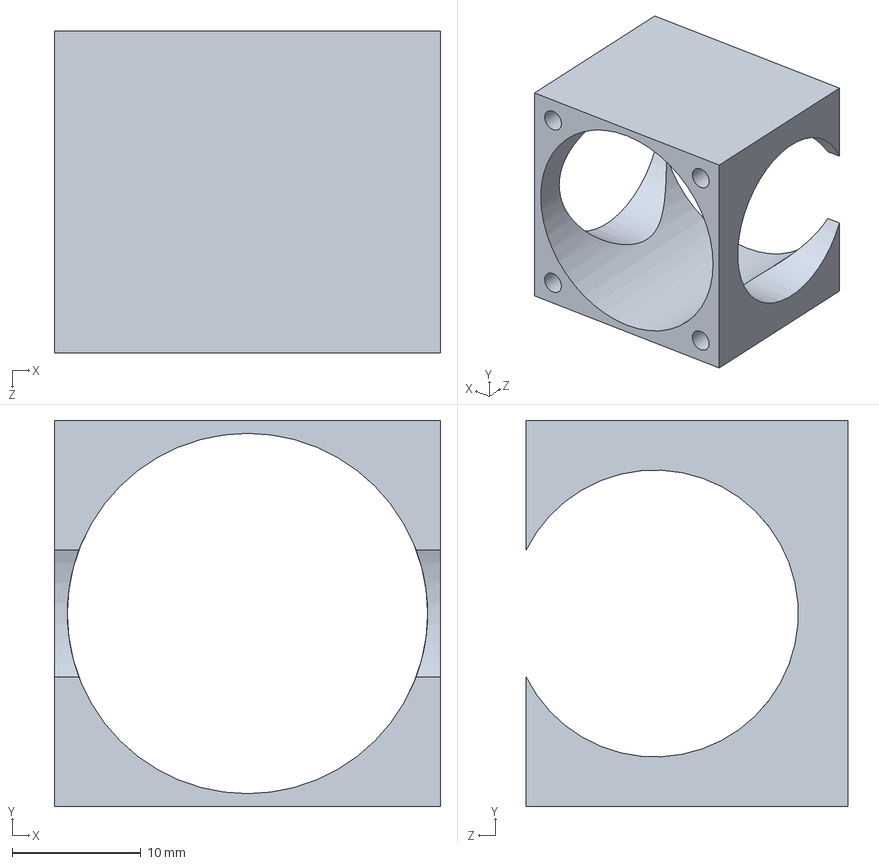
[picture p74: CAD file, 2020-09-15]
SolidWorks/New/风扇固定.SLDPRT
30.0 x 30.0 x 25.0 mm
