abnormal0/3D_Printer/SolidWorks/New/M4垫片.SLDPRT

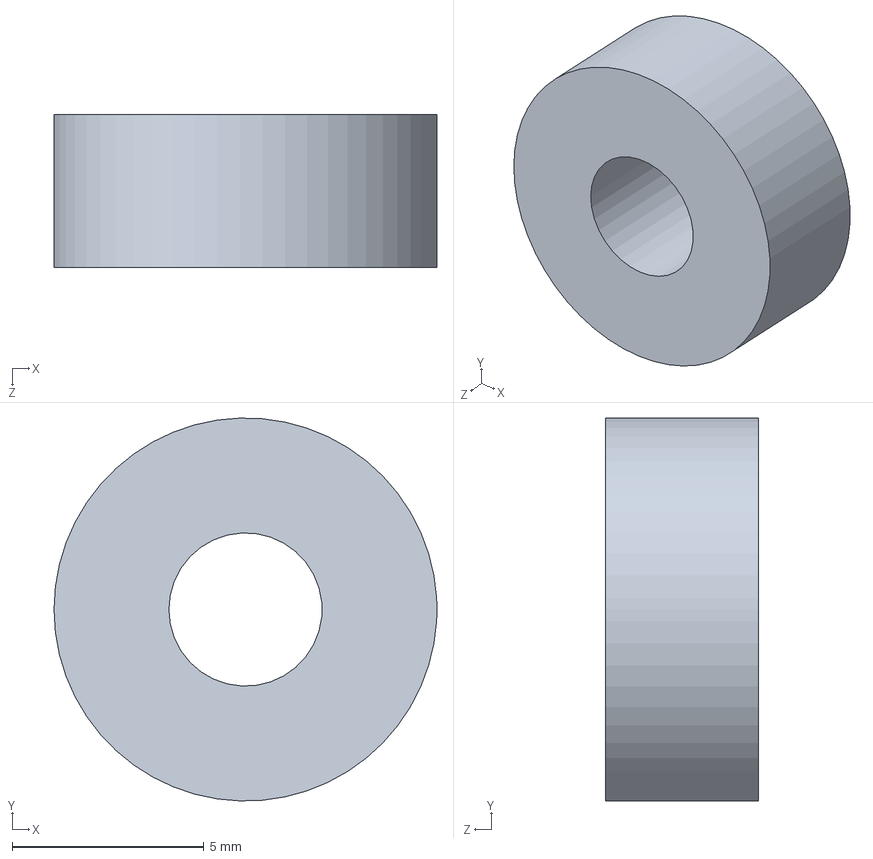
[picture p75: CAD file, 2020-09-15]
SolidWorks/New/M4垫片.SLDPRT
10.0 x 10.00 x 4.00 mm
