abnormal0/3D_Printer/stm32/Project/ArmCpp/Dev/Ntc.h

//
// Created by draw on 19-5-13.
//

#ifndef _NTC_H
#define _NTC_H

#include "Descriptor.h"

const float Ntc_Tab[] =
        {
                1053846.90, 991092.65, 932523.94, 877833.76, 826739.54, 778981.08, 734318.62, 692531.15, 653414.78,
                616781.36,

                582457.13, 550281.58, 520106.32, 491794.13, 465218.03, 440260.47, 416812.55, 394773.36, 374049.37,
                354553.77,

                336206.04, 318931.38, 302660.34, 287328.36, 272875.40, 259245.62, 246387.08, 234251.37, 222793.44,
                211971.29,

                201745.77, 192080.36, 182941.00, 174295.87, 166115.28, 158371.48, 151038.53, 144092.20, 137509.80,
                131270.11,

                125353.26, 119740.65, 114414.85, 109359.52, 104559.36, 100000.00, 95667.96, 91550.61, 87636.05,
                83913.14,

                80371.41, 77000.99, 73792.63, 70737.61, 67827.74, 65055.31, 62413.05, 59894.12, 57492.07, 55200.83,

                53014.67, 50928.19, 48936.30, 47034.18, 45217.30, 43481.37, 41822.34, 40236.39, 38719.90, 37269.46,

                35881.83, 34553.95, 33282.93, 32066.03, 30900.66, 29784.36, 28714.81, 27689.80, 26707.24, 25765.15,

                24861.65, 23994.96, 23163.39, 22365.33, 21599.25, 20863.72, 20157.36, 19478.85, 18826.96, 18200.51,

                17598.37, 17019.48, 16462.83, 15927.44, 15412.39, 14916.82, 14439.89, 13980.80, 13538.80, 13113.16,

                12703.20, 12308.27, 11927.74, 11561.00, 11207.51, 10866.71, 10538.08, 10221.14, 9915.40, 9620.42,

                9335.77, 9061.04, 8795.83, 8539.77, 8292.49, 8053.67, 7822.96, 7600.05, 7384.64, 7176.45,

                6975.20, 6780.62, 6592.46, 6410.49, 6234.46, 6064.16, 5899.37, 5739.89, 5585.53, 5436.09,

                5291.40, 5151.29, 5015.58, 4884.13, 4756.77, 4633.37, 4513.77, 4397.85, 4285.48, 4176.53,

                4070.89, 3968.43, 3869.05, 3772.64, 3679.11, 3588.34, 3500.25, 3414.75, 3331.74, 3251.16,

                3172.90, 3096.91, 3023.09, 2951.39, 2881.73, 2814.04, 2748.26, 2684.32, 2622.18, 2561.76,

                2503.02, 2445.90, 2390.35, 2336.32, 2283.76, 2232.62, 2182.87, 2134.45, 2087.33, 2041.47,

                1996.82, 1953.35, 1911.03, 1869.82, 1829.68, 1790.59, 1752.51, 1715.40, 1679.25, 1644.03,

                1609.70, 1576.24, 1543.63, 1511.83, 1480.83, 1450.61, 1421.13, 1392.39, 1364.35, 1337.00,

                1310.31, 1284.28, 1258.88, 1234.09, 1209.89, 1186.28, 1163.22, 1140.72, 1118.75, 1097.29,

                1076.34, 1055.88, 1035.89, 1016.37, 997.30, 978.67, 960.46, 942.67, 925.29, 908.29,

                891.69, 875.45, 859.58, 844.06, 828.89, 814.05, 799.54, 785.35, 771.47, 757.90,

                744.61, 731.62, 718.90, 706.46, 694.28, 682.37, 670.70, 659.29, 648.11, 637.17,

                626.45, 615.96, 605.69, 595.63, 585.78, 576.13, 566.68, 557.42, 548.35, 539.46,

                530.75, 522.22, 513.86, 505.66, 497.63, 489.75, 482.03, 474.47, 467.05, 459.77,

                452.64, 445.65, 438.79, 432.06, 425.47, 418.99, 412.65, 406.42, 400.31, 394.31,

                388.43, 382.66, 376.99, 371.44, 365.98, 360.62, 355.37, 350.21, 345.14, 340.17,

                335.28, 330.49, 325.78, 321.16, 316.61, 312.15, 307.77, 303.47, 299.24, 295.09,

                291.01, 287.00, 283.06, 279.19, 275.39, 271.65, 267.98, 264.37, 260.82, 257.33,

                253.90, 250.53, 247.22, 243.96, 240.76, 237.61, 234.51, 231.46, 228.47, 225.52,

                222.62, 219.77, 216.97, 214.21, 211.50, 208.83, 206.20, 203.62, 201.07, 198.57,

                196.11, 193.69, 191.30, 188.96, 186.64, 184.37, 182.13, 179.93, 177.76, 175.62,
        };


class Ntc
{

public:
    float Value(float r);
};

extern Ntc Rs;


#endif //ARMCPP_NTC_H
