abnormal0/3D_Printer/stm32/Project/ArmCpp/Dev/InOut.h

//
// Created by draw on 19-5-11.
//

#ifndef _INOUT_H
#define _INOUT_H


#include <Basic.h>

class InOut
{

public:
    void Tog1(void);

    void Beep(bl on);

    void Construct();
};

extern InOut Io;

#endif //ARMCPP_INOUT_H
