abnormal0/3D_Printer/stm32/Project/ArmCpp/MspLib/Msp.h

//
// Created by Nc2016 on 2019/1/10.
//

#ifndef __MSP_H
#define __MSP_H

#include "Stm32f407xx.h"
#include "Basic.h"
#include "Spread.h"

#include "Cortex.h"

#include "Flash.h"
#include "Gpio.h"
#include "Power.h"
#include "Rcc.h"
#include "Tick.h"
#include "Usart.h"
#include "Scb.h"
#include "Nvic.h"
#include "Dma.h"
#include "Tim.h"
#include "Adc.h"
#include "Sdio.h"





#endif
